ryomuk/tangnano-5V/applications/TangNano8080MEM/images/upd8080afc_3MHz.jpg

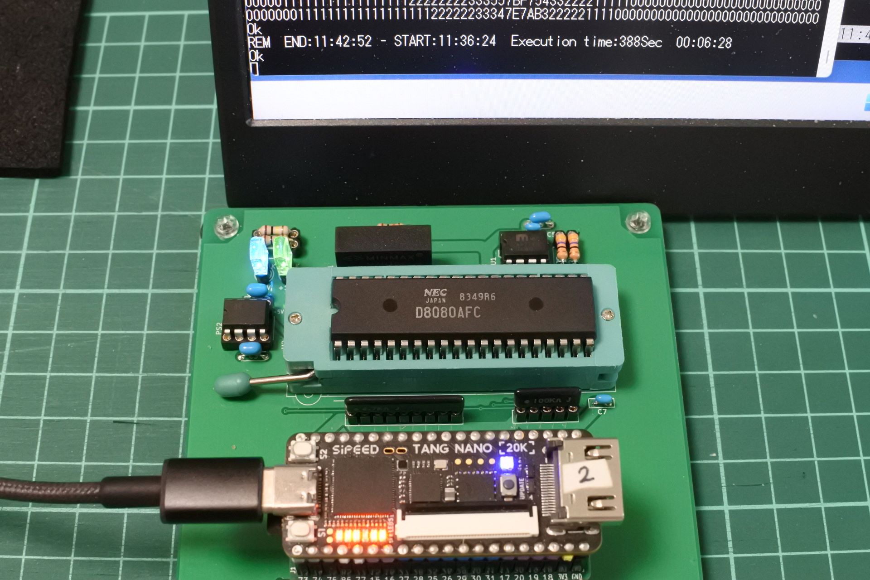
applications/TangNano8080MEM/images/upd8080afc_3MHz.jpg
