ryomuk/tangnano-5V/images/asciiart_12MHz.png

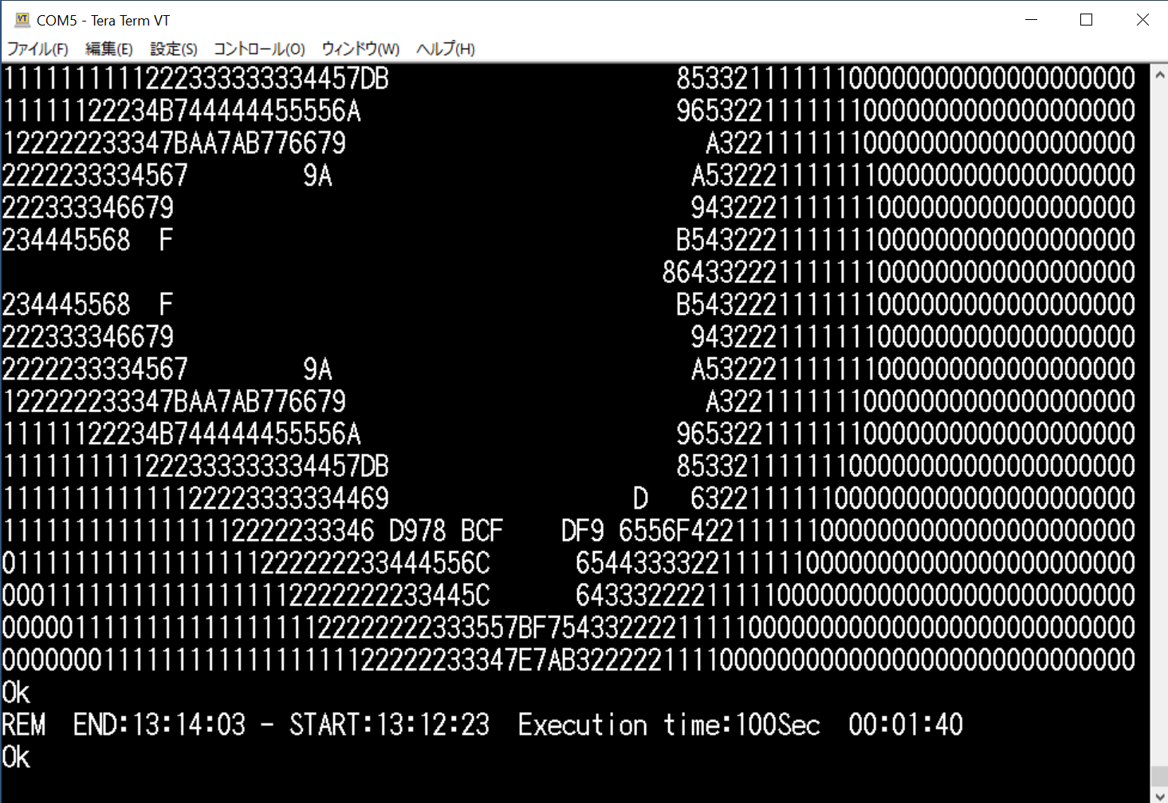
images/asciiart_12MHz.png
