ryomuk/tangnano-5V/images/tn20k5vrev1_1.jpg

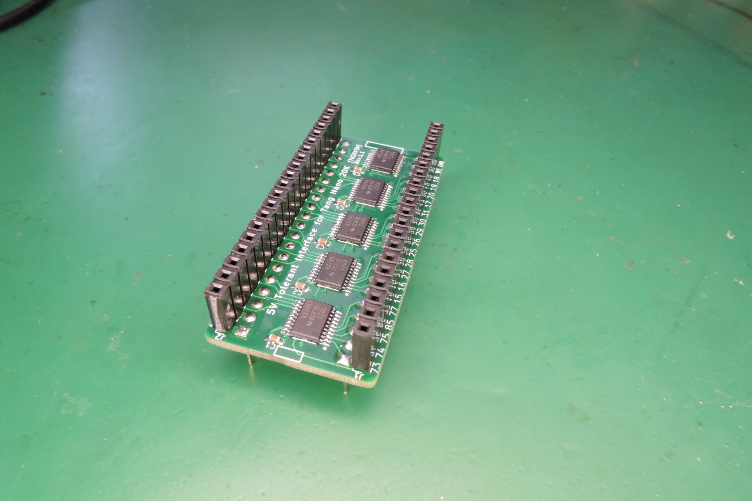
images/tn20k5vrev1_1.jpg
