ryomuk/tangnano-5V/hardware/9k/old/rev2.0/TangNano9K5V_pcb.pdf

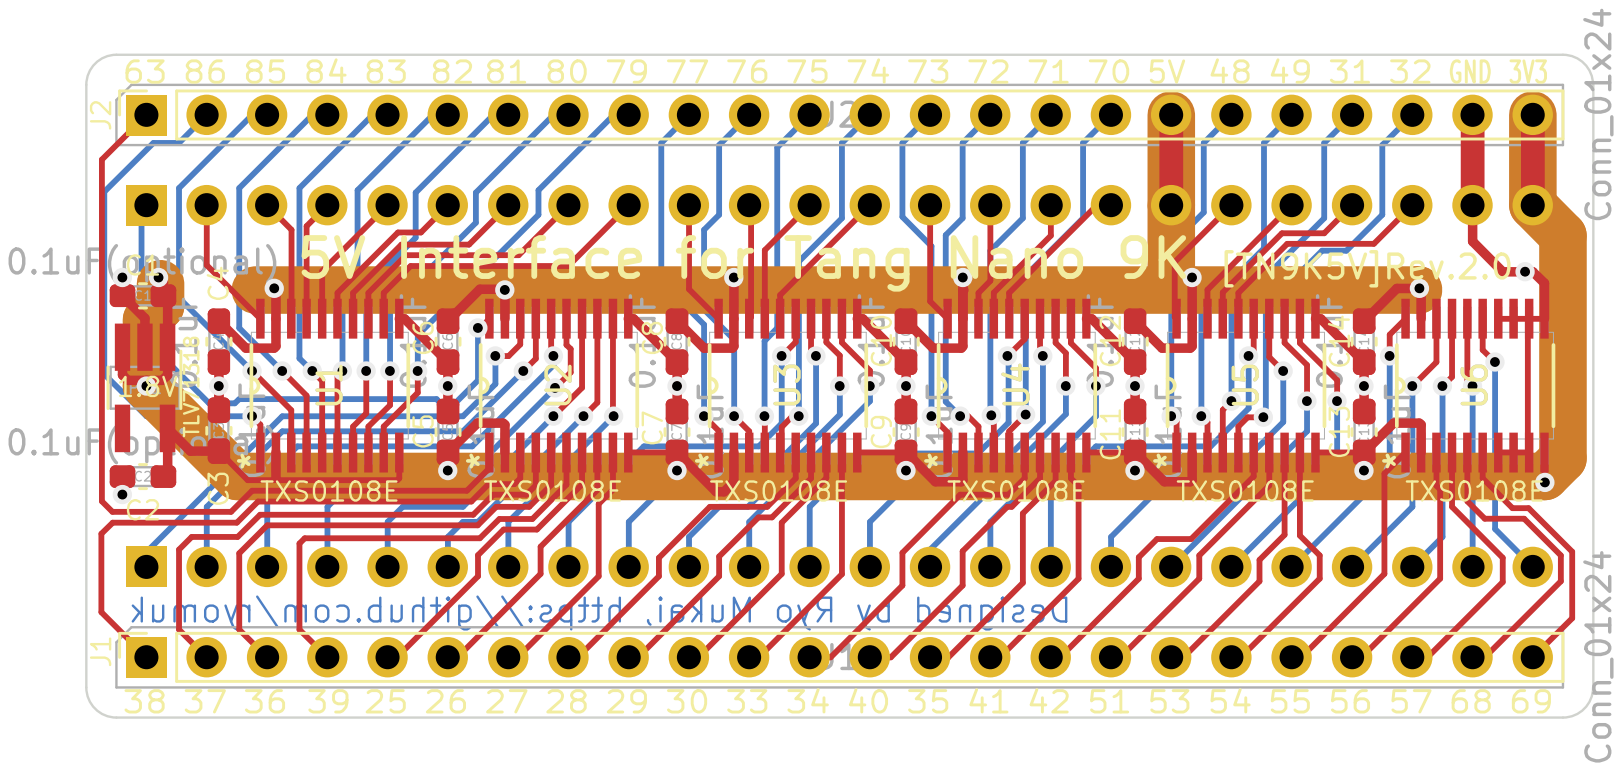
[picture p50: page 1]
