ryomuk/tangnano-5V/hardware/9k/old/rev2.0/TangNano9K5V_sch.pdf

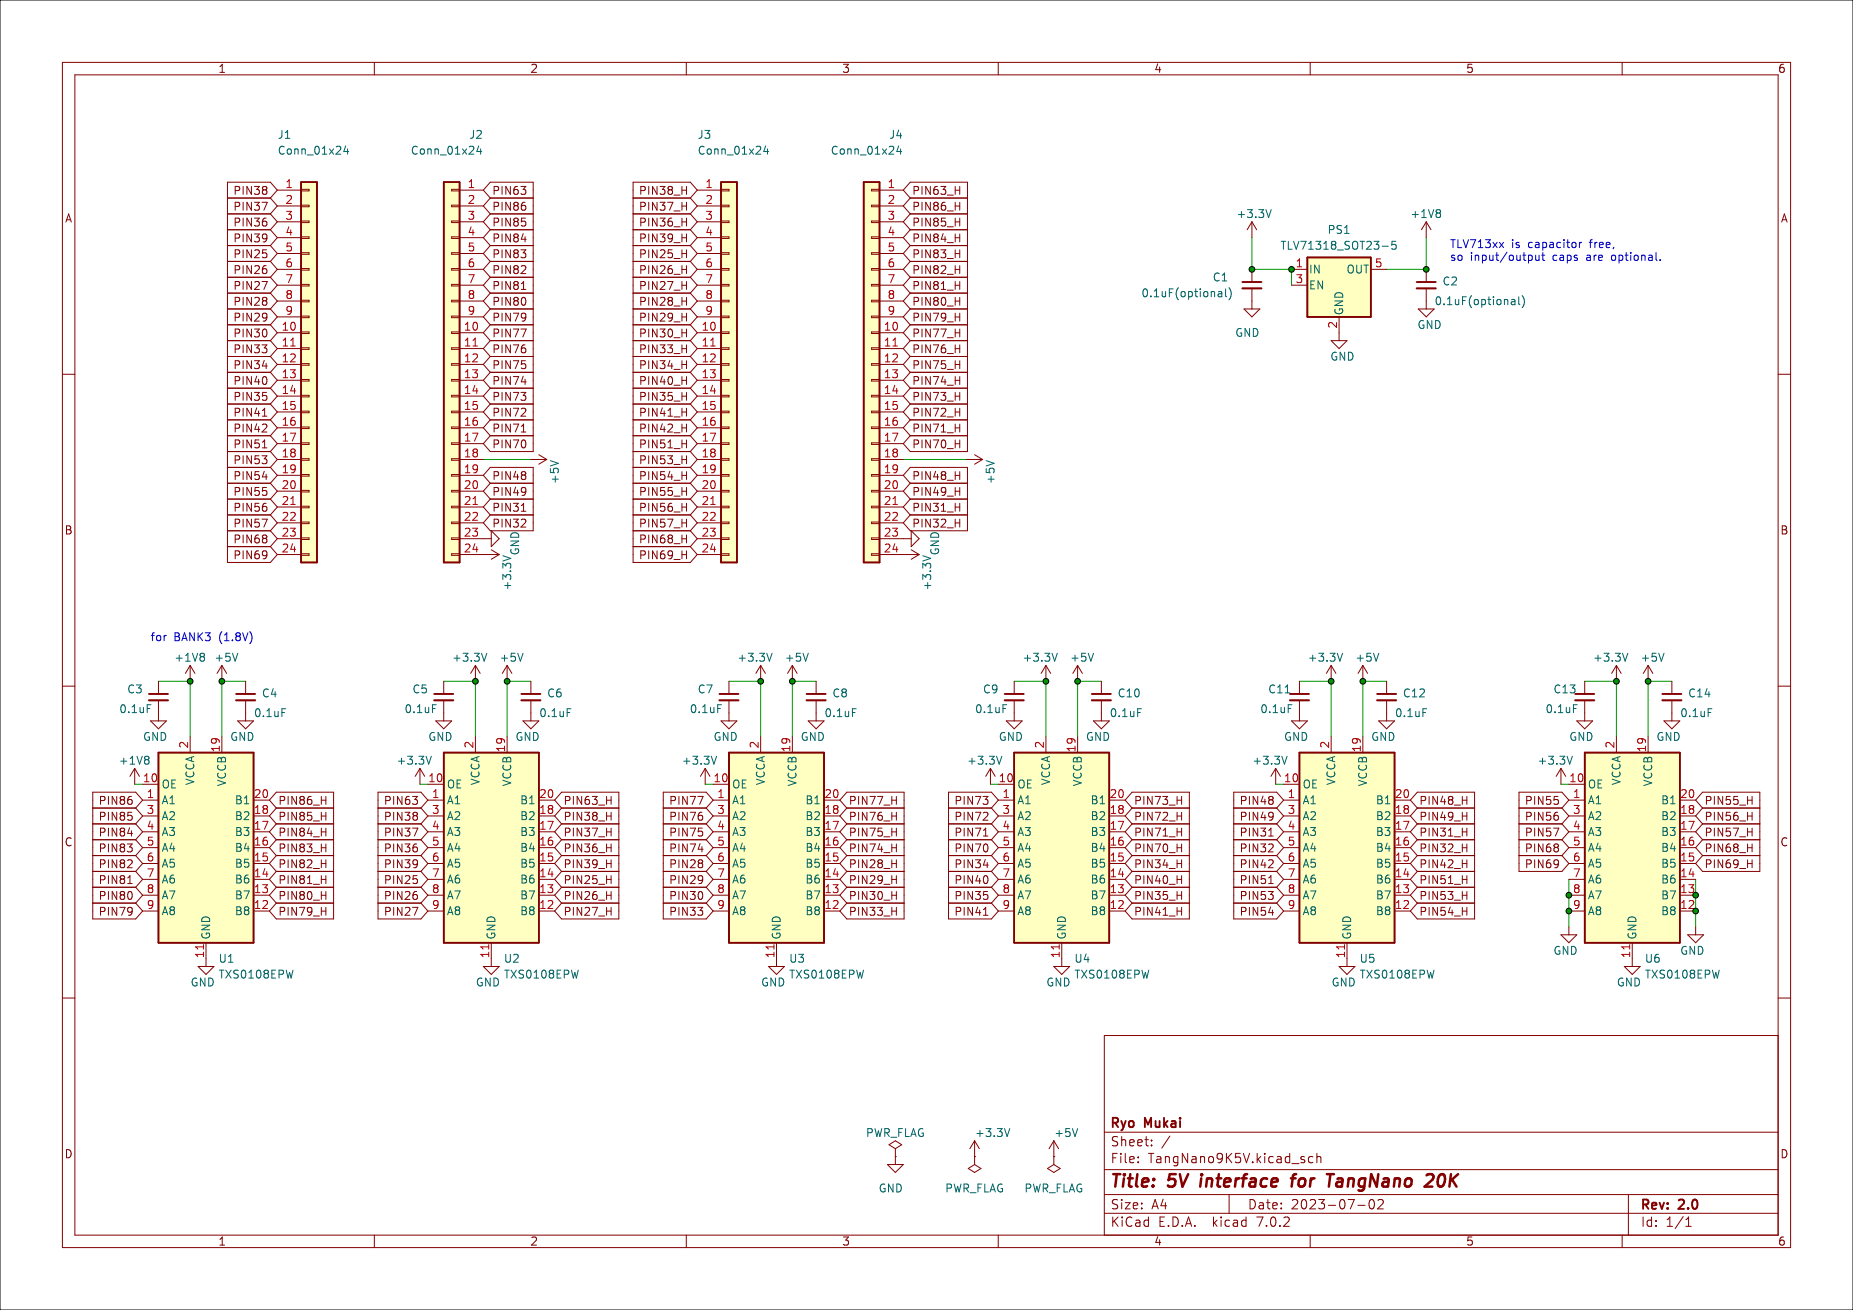
[picture p51: page 1]
