ryomuk/tangnano-5V/hardware/20k/old/rev1.1/TangNano5V_pcb.pdf

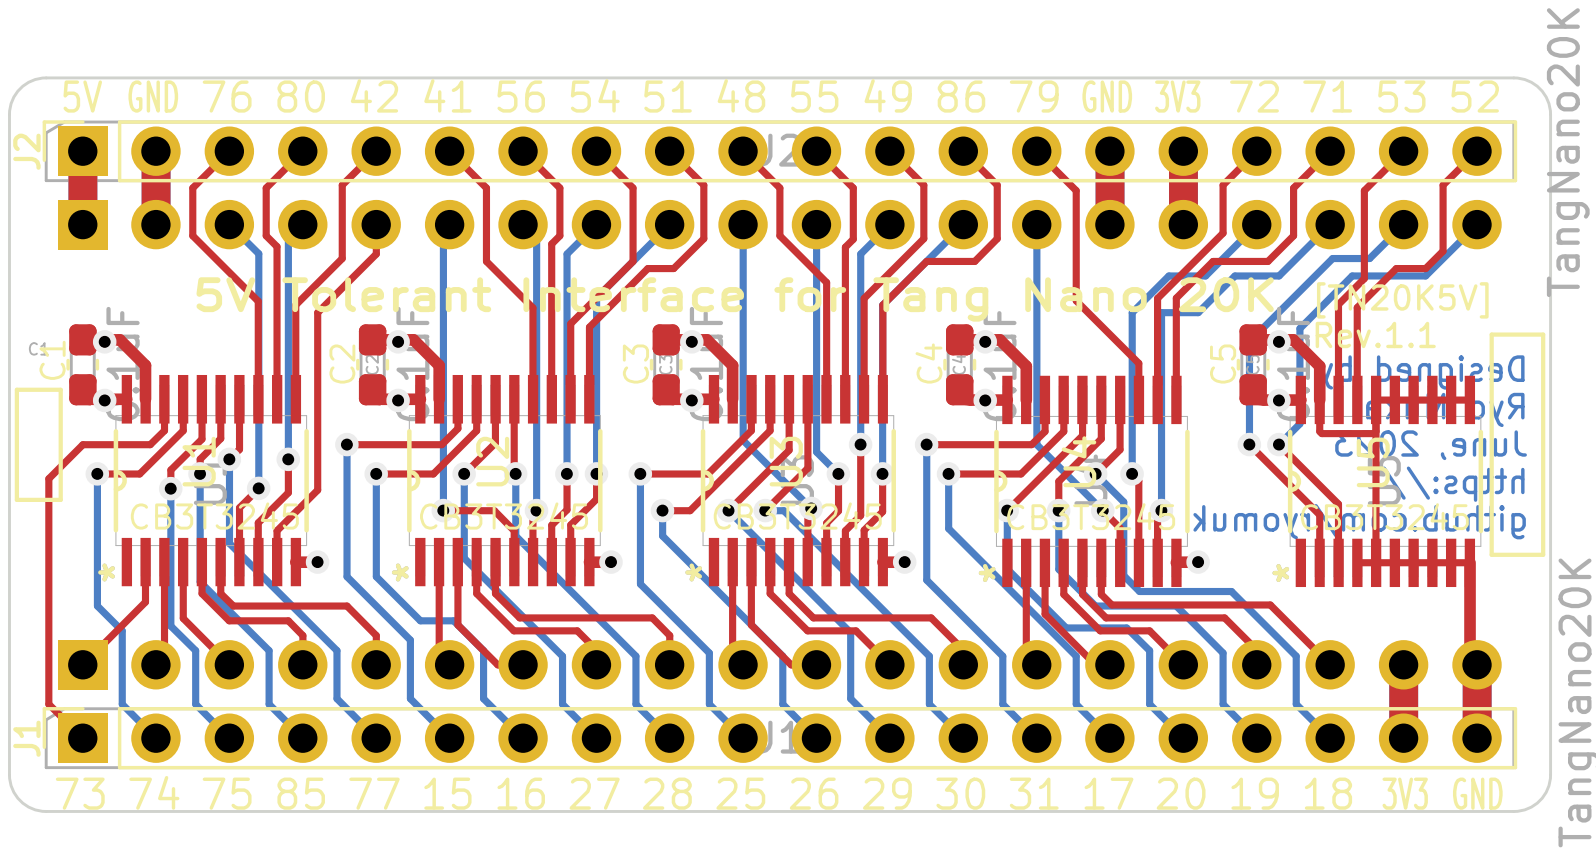
[picture p52: page 1]
