ryomuk/tangnano-5V/applications/TangNano8070MEM/rev1.0/TangNano8070MEM.kicad_sch

## KiCad design applications/TangNano8070MEM/rev1.0/TangNano8070MEM.kicad_sch (2023-07-23)

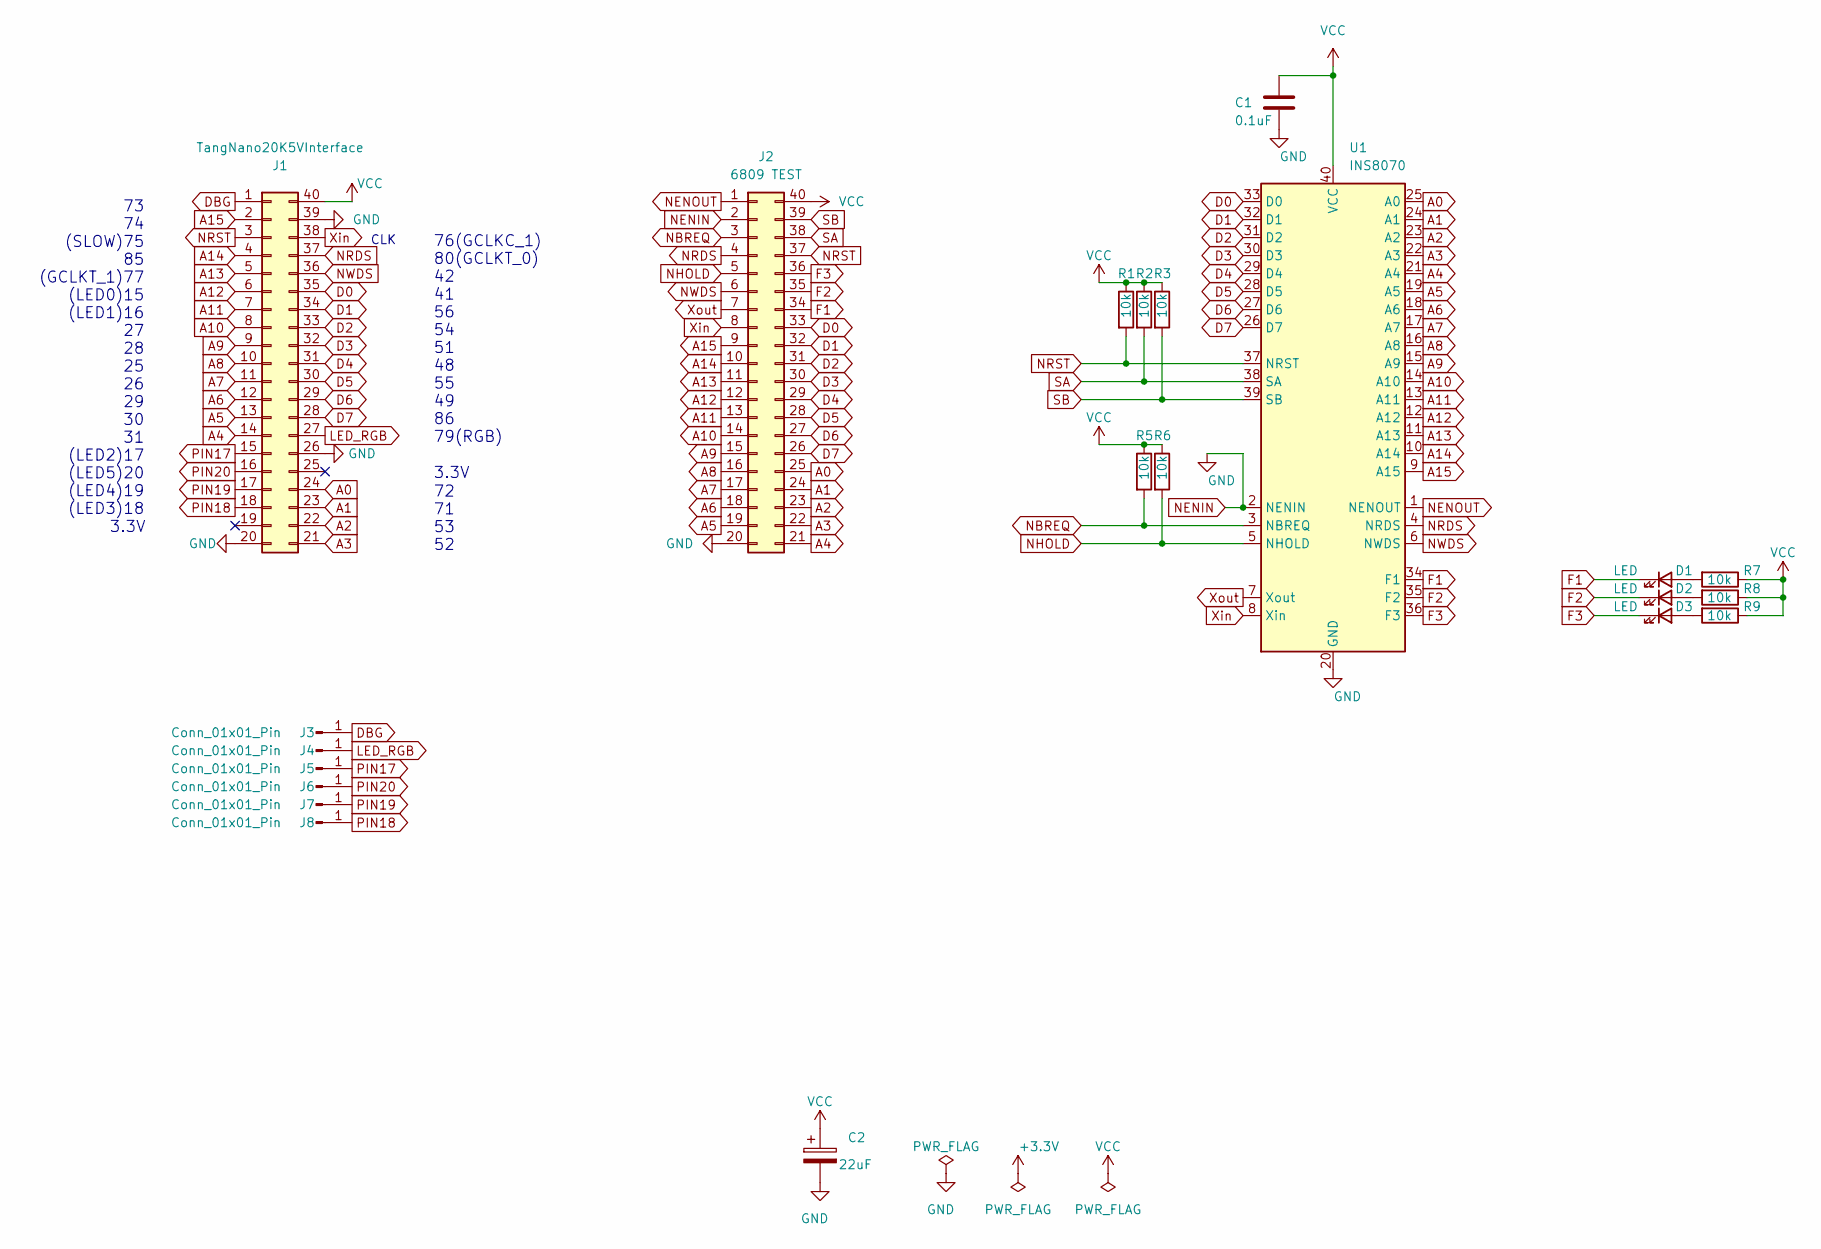
[picture p66: schematic TangNano8070MEM.kicad_sch]

Parts:
C1: 0.1uF; C_Disc_D4.3mm_W1.9mm_P5.00mm
C2: 22uF; CP_Radial_D4.0mm_P1.50mm
D1, D2, D3: LED; LED_D3.0mm
J1: TangNano20K5VInterface; DIP-40_W15.24mm_Socket
J2: 6809 TEST; DIP-40_W20.32mm800mil_Socket
J3, J4, J5, J6, J7, J8: Conn_01x01_Pin; PinHeader_1x01_P2.54mm_Vertical
R1, R2, R3, R5, R6, R7, R8, R9: 10k; R_Axial_DIN0207_L6.3mm_D2.5mm_P7.62mm_Horizontal
U1: INS8070; DIP-40_W15.24mm

Connections:
A0: J1.24, J2.25, U1.25 (A0)
A1: J1.23, J2.24, U1.24 (A1)
A2: J1.22, J2.23, U1.23 (A2)
A3: J1.21, J2.22, U1.22 (A3)
A4: J1.14, J2.21, U1.21 (A4)
A5: J1.13, J2.19, U1.19 (A5)
A6: J1.12, J2.18, U1.18 (A6)
A7: J1.11, J2.17, U1.17 (A7)
A8: J1.10, J2.16, U1.16 (A8)
A9: J1.9, J2.15, U1.15 (A9)
A10: J1.8, J2.14, U1.14 (A10)
A11: J1.7, J2.13, U1.13 (A11)
A12: J1.6, J2.12, U1.12 (A12)
A13: J1.5, J2.11, U1.11 (A13)
A14: J1.4, J2.10, U1.10 (A14)
A15: J1.2, J2.9, U1.9 (A15)
D0: J1.35, J2.33, U1.33 (D0)
D1: J1.34, J2.32, U1.32 (D1)
D2: J1.33, J2.31, U1.31 (D2)
D3: J1.32, J2.30, U1.30 (D3)
D4: J1.31, J2.29, U1.29 (D4)
D5: J1.30, J2.28, U1.28 (D5)
D6: J1.29, J2.27, U1.27 (D6)
D7: J1.28, J2.26, U1.26 (D7)
DBG: J1.1, J3.1
F1: D1.1 (K), J2.34, U1.34 (F1)
F2: D2.1 (K), J2.35, U1.35 (F2)
F3: D3.1 (K), J2.36, U1.36 (F3)
GND: C1.2, C2.2, J1.20, J1.26, J1.39, J2.2, J2.20, U1.2 (NENIN), U1.20 (GND)
LED_RGB: J1.27, J4.1
NBREQ: J2.3, R5.2, U1.3 (NBREQ)
NENOUT: J2.1, U1.1 (NENOUT)
NHOLD: J2.5, R6.2, U1.5 (NHOLD)
NRDS: J1.37, J2.4, U1.4 (NRDS)
NRST: J1.3, J2.37, R1.2, U1.37 (NRST)
NWDS: J1.36, J2.6, U1.6 (NWDS)
unnamed: D1.2 (A), R7.2
unnamed: D2.2 (A), R8.2
unnamed: D3.2 (A), R9.2
PIN17: J1.15, J5.1
PIN18: J1.18, J8.1
PIN19: J1.17, J7.1
PIN20: J1.16, J6.1
SA: J2.38, R2.2, U1.38 (SA)
SB: J2.39, R3.2, U1.39 (SB)
VCC: C1.1, C2.1, J1.40, J2.40, R1.1, R2.1, R3.1, R5.1, R6.1, R7.1, R8.1, R9.1, U1.40 (VCC)
Xin: J1.38, J2.8, U1.8 (Xin)
Xout: J2.7, U1.7 (Xout)

Notes on the sheet:
72 71 53 52
73 74 (SLOW)75 85 (GCLKT_1)77 (LED0)15 (LED1)16 27 28 25 26 29 30 31 (LED2)17 (LED5)20 (LED4)19 (LED3)18
76(GCLKC_1) 80(GCLKT_0) 42 41 56 54 51 48 55 49 86 79(RGB)
3.3V
CLK
