ryomuk/tangnano-5V/applications/9K/TangNanoZ80MEM_9K/breadboard/TangNanoZ80MEM.kicad_sch

## KiCad design applications/9K/TangNanoZ80MEM_9K/breadboard/TangNanoZ80MEM.kicad_sch (2024-04-21)

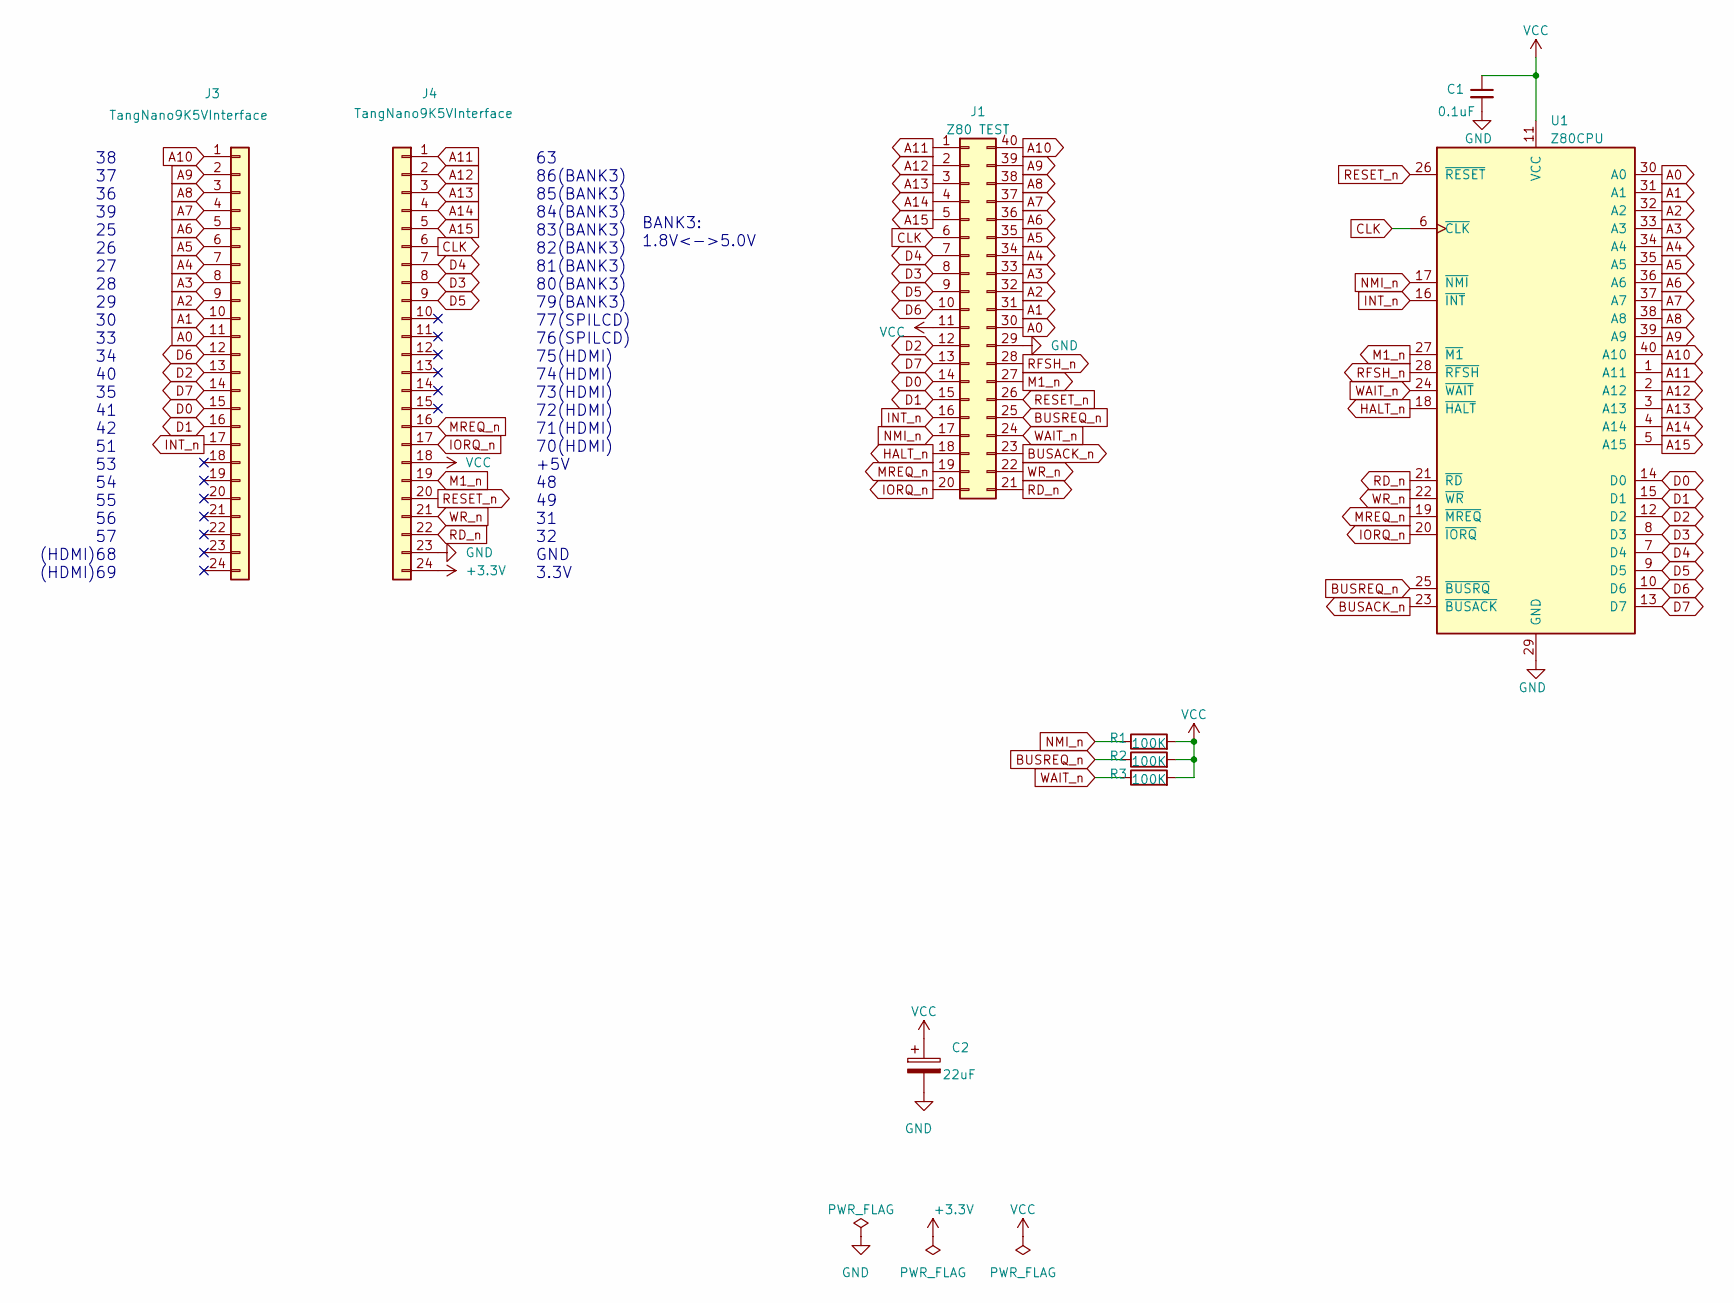
[picture p67: schematic TangNanoZ80MEM.kicad_sch]

Parts:
C1: 0.1uF; C_Disc_D4.3mm_W1.9mm_P5.00mm
C2: 22uF; CP_Radial_D4.0mm_P1.50mm
J1: Z80 TEST; DIP-40_W20.32mm800mil_Socket
J3, J4: TangNano9K5VInterface; PinHeader_1x24_P2.54mm_Vertical
R1, R2, R3: 100K
U1: Z80CPU; DIP-40_W15.24mm_Socket

Connections:
+3.3V: J4.24
A0: J1.30, J3.11, U1.30 (A0)
A1: J1.31, J3.10, U1.31 (A1)
A2: J1.32, J3.9, U1.32 (A2)
A3: J1.33, J3.8, U1.33 (A3)
A4: J1.34, J3.7, U1.34 (A4)
A5: J1.35, J3.6, U1.35 (A5)
A6: J1.36, J3.5, U1.36 (A6)
A7: J1.37, J3.4, U1.37 (A7)
A8: J1.38, J3.3, U1.38 (A8)
A9: J1.39, J3.2, U1.39 (A9)
A10: J1.40, J3.1, U1.40 (A10)
A11: J1.1, J4.1, U1.1 (A11)
A12: J1.2, J4.2, U1.2 (A12)
A13: J1.3, J4.3, U1.3 (A13)
A14: J1.4, J4.4, U1.4 (A14)
A15: J1.5, J4.5, U1.5 (A15)
BUSACK_n: J1.23, U1.23 (~BUSACK)
BUSREQ_n: J1.25, R2.1, U1.25 (~BUSRQ)
CLK: J1.6, J4.6, U1.6 (~CLK)
D0: J1.14, J3.15, U1.14 (D0)
D1: J1.15, J3.16, U1.15 (D1)
D2: J1.12, J3.13, U1.12 (D2)
D3: J1.8, J4.8, U1.8 (D3)
D4: J1.7, J4.7, U1.7 (D4)
D5: J1.9, J4.9, U1.9 (D5)
D6: J1.10, J3.12, U1.10 (D6)
D7: J1.13, J3.14, U1.13 (D7)
GND: C1.2, C2.2, J1.29, J4.23, U1.29 (GND)
HALT_n: J1.18, U1.18 (~HALT)
INT_n: J1.16, J3.17, U1.16 (~INT)
IORQ_n: J1.20, J4.17, U1.20 (~IORQ)
M1_n: J1.27, J4.19, U1.27 (~M1)
MREQ_n: J1.19, J4.16, U1.19 (~MREQ)
NMI_n: J1.17, R1.1, U1.17 (~NMI)
RD_n: J1.21, J4.22, U1.21 (~RD)
RESET_n: J1.26, J4.20, U1.26 (~RESET)
RFSH_n: J1.28, U1.28 (~RFSH)
VCC: C1.1, C2.1, J1.11, J4.18, R1.2, R2.2, R3.2, U1.11 (VCC)
WAIT_n: J1.24, R3.1, U1.24 (~WAIT)
WR_n: J1.22, J4.21, U1.22 (~WR)

Notes on the sheet:
38 37 36 39 25 26 27 28 29 30 33 34 40 35 41 42 51 53 54 55 56 57 (HDMI)68 (HDMI)69
BANK3: 1.8V<->5.0V
63 86(BANK3) 85(BANK3) 84(BANK3) 83(BANK3) 82(BANK3) 81(BANK3) 80(BANK3) 79(BANK3) 77(SPILCD) 76(SPILCD) 75(HDMI) 74(HDMI) 73(HDMI) 72(HDMI) 71(HDMI) 70(HDMI) +5V 48 49 31 32 GND 3.3V
