ryomuk/tangnano-5V/applications/TangNano8080MEM/TangNano8080MEM_project/src/rom.unimon.v

// rom.unimon.v
// to be included from the top module at the comple
//
// This file is generated from 
// unimon-20230319/8080
// https://electrelic.com/electrelic/node/1318
//
// MIT License
// 
// Copyright (c) 2019,2020,2021 Haruo Asano
// 
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
initial
begin
    mem['h0000]=8'hF3; mem['h0001]=8'hC3; mem['h0002]=8'h00; mem['h0003]=8'h01;
    mem['h0004]=8'hFF; mem['h0005]=8'hFF; mem['h0006]=8'hFF; mem['h0007]=8'hFF;
    mem['h0008]=8'hFF; mem['h0009]=8'hFF; mem['h000A]=8'hFF; mem['h000B]=8'hFF;
    mem['h000C]=8'hFF; mem['h000D]=8'hFF; mem['h000E]=8'hFF; mem['h000F]=8'hFF;
    mem['h0010]=8'hC3; mem['h0011]=8'hBC; mem['h0012]=8'h09; mem['h0013]=8'hFF;
    mem['h0014]=8'hFF; mem['h0015]=8'hFF; mem['h0016]=8'hFF; mem['h0017]=8'hFF;
    mem['h0018]=8'hC3; mem['h0019]=8'hA7; mem['h001A]=8'h06; mem['h001B]=8'hFF;
    mem['h001C]=8'hFF; mem['h001D]=8'hFF; mem['h001E]=8'hFF; mem['h001F]=8'hFF;
    mem['h0020]=8'hC3; mem['h0021]=8'hAD; mem['h0022]=8'h09; mem['h0023]=8'hFF;
    mem['h0024]=8'hFF; mem['h0025]=8'hFF; mem['h0026]=8'hFF; mem['h0027]=8'hFF;
    mem['h0028]=8'hC3; mem['h0029]=8'hB7; mem['h002A]=8'h09; mem['h002B]=8'hFF;
    mem['h002C]=8'hFF; mem['h002D]=8'hFF; mem['h002E]=8'hFF; mem['h002F]=8'hFF;
    mem['h0030]=8'hC3; mem['h0031]=8'hB6; mem['h0032]=8'h07; mem['h0033]=8'hFF;
    mem['h0034]=8'hFF; mem['h0035]=8'hFF; mem['h0036]=8'hFF; mem['h0037]=8'hFF;
    mem['h0038]=8'hC3; mem['h0039]=8'hE1; mem['h003A]=8'h07; mem['h003B]=8'hFF;
    mem['h003C]=8'hFF; mem['h003D]=8'hFF; mem['h003E]=8'hFF; mem['h003F]=8'hFF;
    mem['h0040]=8'hFF; mem['h0041]=8'hFF; mem['h0042]=8'hFF; mem['h0043]=8'hFF;
    mem['h0044]=8'hFF; mem['h0045]=8'hFF; mem['h0046]=8'hFF; mem['h0047]=8'hFF;
    mem['h0048]=8'hFF; mem['h0049]=8'hFF; mem['h004A]=8'hFF; mem['h004B]=8'hFF;
    mem['h004C]=8'hFF; mem['h004D]=8'hFF; mem['h004E]=8'hFF; mem['h004F]=8'hFF;
    mem['h0050]=8'hFF; mem['h0051]=8'hFF; mem['h0052]=8'hFF; mem['h0053]=8'hFF;
    mem['h0054]=8'hFF; mem['h0055]=8'hFF; mem['h0056]=8'hFF; mem['h0057]=8'hFF;
    mem['h0058]=8'hFF; mem['h0059]=8'hFF; mem['h005A]=8'hFF; mem['h005B]=8'hFF;
    mem['h005C]=8'hFF; mem['h005D]=8'hFF; mem['h005E]=8'hFF; mem['h005F]=8'hFF;
    mem['h0060]=8'hFF; mem['h0061]=8'hFF; mem['h0062]=8'hFF; mem['h0063]=8'hFF;
    mem['h0064]=8'hFF; mem['h0065]=8'hFF; mem['h0066]=8'hFF; mem['h0067]=8'hFF;
    mem['h0068]=8'hFF; mem['h0069]=8'hFF; mem['h006A]=8'hFF; mem['h006B]=8'hFF;
    mem['h006C]=8'hFF; mem['h006D]=8'hFF; mem['h006E]=8'hFF; mem['h006F]=8'hFF;
    mem['h0070]=8'hFF; mem['h0071]=8'hFF; mem['h0072]=8'hFF; mem['h0073]=8'hFF;
    mem['h0074]=8'hFF; mem['h0075]=8'hFF; mem['h0076]=8'hFF; mem['h0077]=8'hFF;
    mem['h0078]=8'hFF; mem['h0079]=8'hFF; mem['h007A]=8'hFF; mem['h007B]=8'hFF;
    mem['h007C]=8'hFF; mem['h007D]=8'hFF; mem['h007E]=8'hFF; mem['h007F]=8'hFF;
    mem['h0080]=8'hC3; mem['h0081]=8'h00; mem['h0082]=8'h01; mem['h0083]=8'hFF;
    mem['h0084]=8'hFF; mem['h0085]=8'hFF; mem['h0086]=8'hFF; mem['h0087]=8'hFF;
    mem['h0088]=8'hC3; mem['h0089]=8'h75; mem['h008A]=8'h01; mem['h008B]=8'hFF;
    mem['h008C]=8'hFF; mem['h008D]=8'hFF; mem['h008E]=8'hFF; mem['h008F]=8'hFF;
    mem['h0090]=8'hC3; mem['h0091]=8'hBC; mem['h0092]=8'h09; mem['h0093]=8'hFF;
    mem['h0094]=8'hFF; mem['h0095]=8'hFF; mem['h0096]=8'hFF; mem['h0097]=8'hFF;
    mem['h0098]=8'hC3; mem['h0099]=8'hA7; mem['h009A]=8'h06; mem['h009B]=8'hFF;
    mem['h009C]=8'hFF; mem['h009D]=8'hFF; mem['h009E]=8'hFF; mem['h009F]=8'hFF;
    mem['h00A0]=8'hC3; mem['h00A1]=8'hAD; mem['h00A2]=8'h09; mem['h00A3]=8'hFF;
    mem['h00A4]=8'hFF; mem['h00A5]=8'hFF; mem['h00A6]=8'hFF; mem['h00A7]=8'hFF;
    mem['h00A8]=8'hC3; mem['h00A9]=8'hB7; mem['h00AA]=8'h09; mem['h00AB]=8'hFF;
    mem['h00AC]=8'hFF; mem['h00AD]=8'hFF; mem['h00AE]=8'hFF; mem['h00AF]=8'hFF;
    mem['h00B0]=8'hFF; mem['h00B1]=8'hFF; mem['h00B2]=8'hFF; mem['h00B3]=8'hFF;
    mem['h00B4]=8'hFF; mem['h00B5]=8'hFF; mem['h00B6]=8'hFF; mem['h00B7]=8'hFF;
    mem['h00B8]=8'hFF; mem['h00B9]=8'hFF; mem['h00BA]=8'hFF; mem['h00BB]=8'hFF;
    mem['h00BC]=8'hFF; mem['h00BD]=8'hFF; mem['h00BE]=8'hFF; mem['h00BF]=8'hFF;
    mem['h00C0]=8'hFF; mem['h00C1]=8'hFF; mem['h00C2]=8'hFF; mem['h00C3]=8'hFF;
    mem['h00C4]=8'hFF; mem['h00C5]=8'hFF; mem['h00C6]=8'hFF; mem['h00C7]=8'hFF;
    mem['h00C8]=8'hFF; mem['h00C9]=8'hFF; mem['h00CA]=8'hFF; mem['h00CB]=8'hFF;
    mem['h00CC]=8'hFF; mem['h00CD]=8'hFF; mem['h00CE]=8'hFF; mem['h00CF]=8'hFF;
    mem['h00D0]=8'hFF; mem['h00D1]=8'hFF; mem['h00D2]=8'hFF; mem['h00D3]=8'hFF;
    mem['h00D4]=8'hFF; mem['h00D5]=8'hFF; mem['h00D6]=8'hFF; mem['h00D7]=8'hFF;
    mem['h00D8]=8'hFF; mem['h00D9]=8'hFF; mem['h00DA]=8'hFF; mem['h00DB]=8'hFF;
    mem['h00DC]=8'hFF; mem['h00DD]=8'hFF; mem['h00DE]=8'hFF; mem['h00DF]=8'hFF;
    mem['h00E0]=8'hFF; mem['h00E1]=8'hFF; mem['h00E2]=8'hFF; mem['h00E3]=8'hFF;
    mem['h00E4]=8'hFF; mem['h00E5]=8'hFF; mem['h00E6]=8'hFF; mem['h00E7]=8'hFF;
    mem['h00E8]=8'hFF; mem['h00E9]=8'hFF; mem['h00EA]=8'hFF; mem['h00EB]=8'hFF;
    mem['h00EC]=8'hFF; mem['h00ED]=8'hFF; mem['h00EE]=8'hFF; mem['h00EF]=8'hFF;
    mem['h00F0]=8'hFF; mem['h00F1]=8'hFF; mem['h00F2]=8'hFF; mem['h00F3]=8'hFF;
    mem['h00F4]=8'hFF; mem['h00F5]=8'hFF; mem['h00F6]=8'hFF; mem['h00F7]=8'hFF;
    mem['h00F8]=8'hFF; mem['h00F9]=8'hFF; mem['h00FA]=8'hFF; mem['h00FB]=8'hFF;
    mem['h00FC]=8'hFF; mem['h00FD]=8'hFF; mem['h00FE]=8'hFF; mem['h00FF]=8'hFF;
    mem['h0100]=8'h31; mem['h0101]=8'h00; mem['h0102]=8'h00; mem['h0103]=8'hCD;
    mem['h0104]=8'h94; mem['h0105]=8'h09; mem['h0106]=8'h21; mem['h0107]=8'h00;
    mem['h0108]=8'h80; mem['h0109]=8'h22; mem['h010A]=8'h10; mem['h010B]=8'hFF;
    mem['h010C]=8'h22; mem['h010D]=8'h17; mem['h010E]=8'hFF; mem['h010F]=8'h22;
    mem['h0110]=8'h15; mem['h0111]=8'hFF; mem['h0112]=8'h3E; mem['h0113]=8'h49;
    mem['h0114]=8'h32; mem['h0115]=8'h19; mem['h0116]=8'hFF; mem['h0117]=8'hAF;
    mem['h0118]=8'h32; mem['h0119]=8'h1B; mem['h011A]=8'hFF; mem['h011B]=8'h21;
    mem['h011C]=8'h1C; mem['h011D]=8'hFF; mem['h011E]=8'h0E; mem['h011F]=8'h0C;
    mem['h0120]=8'hAF; mem['h0121]=8'h77; mem['h0122]=8'h23; mem['h0123]=8'h0D;
    mem['h0124]=8'hC2; mem['h0125]=8'h21; mem['h0126]=8'h01; mem['h0127]=8'h21;
    mem['h0128]=8'h00; mem['h0129]=8'h00; mem['h012A]=8'h22; mem['h012B]=8'h23;
    mem['h012C]=8'hFF; mem['h012D]=8'h21; mem['h012E]=8'h00; mem['h012F]=8'h80;
    mem['h0130]=8'h22; mem['h0131]=8'h25; mem['h0132]=8'hFF; mem['h0133]=8'h21;
    mem['h0134]=8'h12; mem['h0135]=8'h08; mem['h0136]=8'hCD; mem['h0137]=8'hA7;
    mem['h0138]=8'h06; mem['h0139]=8'h3E; mem['h013A]=8'h7F; mem['h013B]=8'h3C;
    mem['h013C]=8'hEA; mem['h013D]=8'h6A; mem['h013E]=8'h01; mem['h013F]=8'hF5;
    mem['h0140]=8'hC1; mem['h0141]=8'h79; mem['h0142]=8'hE6; mem['h0143]=8'h08;
    mem['h0144]=8'hC2; mem['h0145]=8'h5A; mem['h0146]=8'h01; mem['h0147]=8'h21;
    mem['h0148]=8'hFF; mem['h0149]=8'hFF; mem['h014A]=8'h23; mem['h014B]=8'hF5;
    mem['h014C]=8'hC1; mem['h014D]=8'h79; mem['h014E]=8'hE6; mem['h014F]=8'h20;
    mem['h0150]=8'hC2; mem['h0151]=8'h62; mem['h0152]=8'h01; mem['h0153]=8'h21;
    mem['h0154]=8'h74; mem['h0155]=8'h08; mem['h0156]=8'hAF; mem['h0157]=8'hC3;
    mem['h0158]=8'h6F; mem['h0159]=8'h01; mem['h015A]=8'h21; mem['h015B]=8'h7C;
    mem['h015C]=8'h08; mem['h015D]=8'h3E; mem['h015E]=8'h01; mem['h015F]=8'hC3;
    mem['h0160]=8'h6F; mem['h0161]=8'h01; mem['h0162]=8'h21; mem['h0163]=8'h87;
    mem['h0164]=8'h08; mem['h0165]=8'h3E; mem['h0166]=8'h02; mem['h0167]=8'hC3;
    mem['h0168]=8'h6F; mem['h0169]=8'h01; mem['h016A]=8'h21; mem['h016B]=8'h8F;
    mem['h016C]=8'h08; mem['h016D]=8'h3E; mem['h016E]=8'h10; mem['h016F]=8'h32;
    mem['h0170]=8'h1B; mem['h0171]=8'hFF; mem['h0172]=8'hCD; mem['h0173]=8'hA7;
    mem['h0174]=8'h06; mem['h0175]=8'h21; mem['h0176]=8'h2D; mem['h0177]=8'h08;
    mem['h0178]=8'hCD; mem['h0179]=8'hA7; mem['h017A]=8'h06; mem['h017B]=8'hCD;
    mem['h017C]=8'h02; mem['h017D]=8'h07; mem['h017E]=8'h21; mem['h017F]=8'h00;
    mem['h0180]=8'hFF; mem['h0181]=8'hCD; mem['h0182]=8'h58; mem['h0183]=8'h07;
    mem['h0184]=8'hCD; mem['h0185]=8'h60; mem['h0186]=8'h07; mem['h0187]=8'hB7;
    mem['h0188]=8'hCA; mem['h0189]=8'h75; mem['h018A]=8'h01; mem['h018B]=8'hFE;
    mem['h018C]=8'h44; mem['h018D]=8'hCA; mem['h018E]=8'hBC; mem['h018F]=8'h01;
    mem['h0190]=8'hFE; mem['h0191]=8'h47; mem['h0192]=8'hCA; mem['h0193]=8'hE4;
    mem['h0194]=8'h02; mem['h0195]=8'hFE; mem['h0196]=8'h53; mem['h0197]=8'hCA;
    mem['h0198]=8'h1A; mem['h0199]=8'h03; mem['h019A]=8'hFE; mem['h019B]=8'h4C;
    mem['h019C]=8'hCA; mem['h019D]=8'h87; mem['h019E]=8'h03; mem['h019F]=8'hFE;
    mem['h01A0]=8'h50; mem['h01A1]=8'hCA; mem['h01A2]=8'h6D; mem['h01A3]=8'h04;
    mem['h01A4]=8'hFE; mem['h01A5]=8'h49; mem['h01A6]=8'hCA; mem['h01A7]=8'h75;
    mem['h01A8]=8'h05; mem['h01A9]=8'hFE; mem['h01AA]=8'h4F; mem['h01AB]=8'hCA;
    mem['h01AC]=8'h9F; mem['h01AD]=8'h05; mem['h01AE]=8'hFE; mem['h01AF]=8'h52;
    mem['h01B0]=8'hCA; mem['h01B1]=8'hDA; mem['h01B2]=8'h05; mem['h01B3]=8'h21;
    mem['h01B4]=8'h30; mem['h01B5]=8'h08; mem['h01B6]=8'hCD; mem['h01B7]=8'hA7;
    mem['h01B8]=8'h06; mem['h01B9]=8'hC3; mem['h01BA]=8'h75; mem['h01BB]=8'h01;
    mem['h01BC]=8'h23; mem['h01BD]=8'hCD; mem['h01BE]=8'h58; mem['h01BF]=8'h07;
    mem['h01C0]=8'hCD; mem['h01C1]=8'h69; mem['h01C2]=8'h07; mem['h01C3]=8'h79;
    mem['h01C4]=8'hB7; mem['h01C5]=8'hC2; mem['h01C6]=8'hDD; mem['h01C7]=8'h01;
    mem['h01C8]=8'hCD; mem['h01C9]=8'h58; mem['h01CA]=8'h07; mem['h01CB]=8'h7E;
    mem['h01CC]=8'hB7; mem['h01CD]=8'hC2; mem['h01CE]=8'hB3; mem['h01CF]=8'h01;
    mem['h01D0]=8'h2A; mem['h01D1]=8'h10; mem['h01D2]=8'hFF; mem['h01D3]=8'h01;
    mem['h01D4]=8'h80; mem['h01D5]=8'h00; mem['h01D6]=8'h09; mem['h01D7]=8'h22;
    mem['h01D8]=8'h12; mem['h01D9]=8'hFF; mem['h01DA]=8'hC3; mem['h01DB]=8'h13;
    mem['h01DC]=8'h02; mem['h01DD]=8'hEB; mem['h01DE]=8'h22; mem['h01DF]=8'h10;
    mem['h01E0]=8'hFF; mem['h01E1]=8'hEB; mem['h01E2]=8'hCD; mem['h01E3]=8'h58;
    mem['h01E4]=8'h07; mem['h01E5]=8'h7E; mem['h01E6]=8'hFE; mem['h01E7]=8'h2C;
    mem['h01E8]=8'hCA; mem['h01E9]=8'hF9; mem['h01EA]=8'h01; mem['h01EB]=8'hB7;
    mem['h01EC]=8'hC2; mem['h01ED]=8'hB3; mem['h01EE]=8'h01; mem['h01EF]=8'h21;
    mem['h01F0]=8'h80; mem['h01F1]=8'h00; mem['h01F2]=8'h19; mem['h01F3]=8'h22;
    mem['h01F4]=8'h12; mem['h01F5]=8'hFF; mem['h01F6]=8'hC3; mem['h01F7]=8'h13;
    mem['h01F8]=8'h02; mem['h01F9]=8'h23; mem['h01FA]=8'hCD; mem['h01FB]=8'h58;
    mem['h01FC]=8'h07; mem['h01FD]=8'hCD; mem['h01FE]=8'h69; mem['h01FF]=8'h07;
    mem['h0200]=8'hCD; mem['h0201]=8'h58; mem['h0202]=8'h07; mem['h0203]=8'h79;
    mem['h0204]=8'hB7; mem['h0205]=8'hCA; mem['h0206]=8'hB3; mem['h0207]=8'h01;
    mem['h0208]=8'h7E; mem['h0209]=8'hB7; mem['h020A]=8'hC2; mem['h020B]=8'hB3;
    mem['h020C]=8'h01; mem['h020D]=8'h13; mem['h020E]=8'hEB; mem['h020F]=8'h22;
    mem['h0210]=8'h12; mem['h0211]=8'hFF; mem['h0212]=8'hEB; mem['h0213]=8'h2A;
    mem['h0214]=8'h10; mem['h0215]=8'hFF; mem['h0216]=8'h3E; mem['h0217]=8'hF0;
    mem['h0218]=8'hA5; mem['h0219]=8'h6F; mem['h021A]=8'hAF; mem['h021B]=8'h32;
    mem['h021C]=8'h14; mem['h021D]=8'hFF; mem['h021E]=8'hE5; mem['h021F]=8'hCD;
    mem['h0220]=8'h47; mem['h0221]=8'h02; mem['h0222]=8'hE1; mem['h0223]=8'h01;
    mem['h0224]=8'h10; mem['h0225]=8'h00; mem['h0226]=8'h09; mem['h0227]=8'hCD;
    mem['h0228]=8'hB7; mem['h0229]=8'h09; mem['h022A]=8'hC2; mem['h022B]=8'h3E;
    mem['h022C]=8'h02; mem['h022D]=8'h3A; mem['h022E]=8'h14; mem['h022F]=8'hFF;
    mem['h0230]=8'hFE; mem['h0231]=8'h02; mem['h0232]=8'hDA; mem['h0233]=8'h1E;
    mem['h0234]=8'h02; mem['h0235]=8'h2A; mem['h0236]=8'h12; mem['h0237]=8'hFF;
    mem['h0238]=8'h22; mem['h0239]=8'h10; mem['h023A]=8'hFF; mem['h023B]=8'hC3;
    mem['h023C]=8'h75; mem['h023D]=8'h01; mem['h023E]=8'hCD; mem['h023F]=8'hAD;
    mem['h0240]=8'h09; mem['h0241]=8'h22; mem['h0242]=8'h10; mem['h0243]=8'hFF;
    mem['h0244]=8'hC3; mem['h0245]=8'h75; mem['h0246]=8'h01; mem['h0247]=8'hCD;
    mem['h0248]=8'hB1; mem['h0249]=8'h06; mem['h024A]=8'hE5; mem['h024B]=8'h21;
    mem['h024C]=8'h38; mem['h024D]=8'h08; mem['h024E]=8'hCD; mem['h024F]=8'hA7;
    mem['h0250]=8'h06; mem['h0251]=8'h21; mem['h0252]=8'h00; mem['h0253]=8'hFF;
    mem['h0254]=8'h22; mem['h0255]=8'h28; mem['h0256]=8'hFF; mem['h0257]=8'hE1;
    mem['h0258]=8'h06; mem['h0259]=8'h10; mem['h025A]=8'hCD; mem['h025B]=8'h8A;
    mem['h025C]=8'h02; mem['h025D]=8'h05; mem['h025E]=8'hC2; mem['h025F]=8'h5A;
    mem['h0260]=8'h02; mem['h0261]=8'h21; mem['h0262]=8'h3B; mem['h0263]=8'h08;
    mem['h0264]=8'hCD; mem['h0265]=8'hA7; mem['h0266]=8'h06; mem['h0267]=8'h21;
    mem['h0268]=8'h00; mem['h0269]=8'hFF; mem['h026A]=8'h06; mem['h026B]=8'h10;
    mem['h026C]=8'h7E; mem['h026D]=8'h23; mem['h026E]=8'hFE; mem['h026F]=8'h20;
    mem['h0270]=8'hDA; mem['h0271]=8'h7E; mem['h0272]=8'h02; mem['h0273]=8'hFE;
    mem['h0274]=8'h7F; mem['h0275]=8'hD2; mem['h0276]=8'h7E; mem['h0277]=8'h02;
    mem['h0278]=8'hCD; mem['h0279]=8'hBC; mem['h027A]=8'h09; mem['h027B]=8'hC3;
    mem['h027C]=8'h83; mem['h027D]=8'h02; mem['h027E]=8'h3E; mem['h027F]=8'h2E;
    mem['h0280]=8'hCD; mem['h0281]=8'hBC; mem['h0282]=8'h09; mem['h0283]=8'h05;
    mem['h0284]=8'hC2; mem['h0285]=8'h6C; mem['h0286]=8'h02; mem['h0287]=8'hC3;
    mem['h0288]=8'hF8; mem['h0289]=8'h06; mem['h028A]=8'h3E; mem['h028B]=8'h20;
    mem['h028C]=8'hCD; mem['h028D]=8'hBC; mem['h028E]=8'h09; mem['h028F]=8'h3A;
    mem['h0290]=8'h14; mem['h0291]=8'hFF; mem['h0292]=8'hB7; mem['h0293]=8'hC2;
    mem['h0294]=8'hBD; mem['h0295]=8'h02; mem['h0296]=8'h3A; mem['h0297]=8'h10;
    mem['h0298]=8'hFF; mem['h0299]=8'hBD; mem['h029A]=8'hC2; mem['h029B]=8'hA4;
    mem['h029C]=8'h02; mem['h029D]=8'h3A; mem['h029E]=8'h11; mem['h029F]=8'hFF;
    mem['h02A0]=8'hBC; mem['h02A1]=8'hCA; mem['h02A2]=8'hB8; mem['h02A3]=8'h02;
    mem['h02A4]=8'h3E; mem['h02A5]=8'h20; mem['h02A6]=8'hCD; mem['h02A7]=8'hBC;
    mem['h02A8]=8'h09; mem['h02A9]=8'hCD; mem['h02AA]=8'hBC; mem['h02AB]=8'h09;
    mem['h02AC]=8'hE5; mem['h02AD]=8'h2A; mem['h02AE]=8'h28; mem['h02AF]=8'hFF;
    mem['h02B0]=8'h77; mem['h02B1]=8'h23; mem['h02B2]=8'h22; mem['h02B3]=8'h28;
    mem['h02B4]=8'hFF; mem['h02B5]=8'hE1; mem['h02B6]=8'h23; mem['h02B7]=8'hC9;
    mem['h02B8]=8'h3E; mem['h02B9]=8'h01; mem['h02BA]=8'h32; mem['h02BB]=8'h14;
    mem['h02BC]=8'hFF; mem['h02BD]=8'h3A; mem['h02BE]=8'h14; mem['h02BF]=8'hFF;
    mem['h02C0]=8'hFE; mem['h02C1]=8'h01; mem['h02C2]=8'hC2; mem['h02C3]=8'hA4;
    mem['h02C4]=8'h02; mem['h02C5]=8'h7E; mem['h02C6]=8'hE5; mem['h02C7]=8'h2A;
    mem['h02C8]=8'h28; mem['h02C9]=8'hFF; mem['h02CA]=8'h77; mem['h02CB]=8'h23;
    mem['h02CC]=8'h22; mem['h02CD]=8'h28; mem['h02CE]=8'hFF; mem['h02CF]=8'hE1;
    mem['h02D0]=8'hCD; mem['h02D1]=8'hB6; mem['h02D2]=8'h06; mem['h02D3]=8'h23;
    mem['h02D4]=8'h3A; mem['h02D5]=8'h12; mem['h02D6]=8'hFF; mem['h02D7]=8'hBD;
    mem['h02D8]=8'hC0; mem['h02D9]=8'h3A; mem['h02DA]=8'h13; mem['h02DB]=8'hFF;
    mem['h02DC]=8'hBC; mem['h02DD]=8'hC0; mem['h02DE]=8'h3E; mem['h02DF]=8'h02;
    mem['h02E0]=8'h32; mem['h02E1]=8'h14; mem['h02E2]=8'hFF; mem['h02E3]=8'hC9;
    mem['h02E4]=8'h23; mem['h02E5]=8'hCD; mem['h02E6]=8'h58; mem['h02E7]=8'h07;
    mem['h02E8]=8'hCD; mem['h02E9]=8'h69; mem['h02EA]=8'h07; mem['h02EB]=8'h7E;
    mem['h02EC]=8'hB7; mem['h02ED]=8'hC2; mem['h02EE]=8'hB3; mem['h02EF]=8'h01;
    mem['h02F0]=8'h79; mem['h02F1]=8'hB7; mem['h02F2]=8'hCA; mem['h02F3]=8'hFA;
    mem['h02F4]=8'h02; mem['h02F5]=8'h62; mem['h02F6]=8'h6B; mem['h02F7]=8'h22;
    mem['h02F8]=8'h25; mem['h02F9]=8'hFF; mem['h02FA]=8'h2A; mem['h02FB]=8'h23;
    mem['h02FC]=8'hFF; mem['h02FD]=8'hF9; mem['h02FE]=8'h2A; mem['h02FF]=8'h25;
    mem['h0300]=8'hFF; mem['h0301]=8'hE5; mem['h0302]=8'h3A; mem['h0303]=8'h27;
    mem['h0304]=8'hFF; mem['h0305]=8'h4F; mem['h0306]=8'h3A; mem['h0307]=8'h1C;
    mem['h0308]=8'hFF; mem['h0309]=8'h47; mem['h030A]=8'hC5; mem['h030B]=8'h21;
    mem['h030C]=8'h1D; mem['h030D]=8'hFF; mem['h030E]=8'h4E; mem['h030F]=8'h23;
    mem['h0310]=8'h46; mem['h0311]=8'h23; mem['h0312]=8'h5E; mem['h0313]=8'h23;
    mem['h0314]=8'h56; mem['h0315]=8'h2A; mem['h0316]=8'h21; mem['h0317]=8'hFF;
    mem['h0318]=8'hF1; mem['h0319]=8'hC9; mem['h031A]=8'h23; mem['h031B]=8'hCD;
    mem['h031C]=8'h58; mem['h031D]=8'h07; mem['h031E]=8'hCD; mem['h031F]=8'h69;
    mem['h0320]=8'h07; mem['h0321]=8'hCD; mem['h0322]=8'h58; mem['h0323]=8'h07;
    mem['h0324]=8'h7E; mem['h0325]=8'hB7; mem['h0326]=8'hC2; mem['h0327]=8'hB3;
    mem['h0328]=8'h01; mem['h0329]=8'hEB; mem['h032A]=8'h79; mem['h032B]=8'hB7;
    mem['h032C]=8'hC2; mem['h032D]=8'h32; mem['h032E]=8'h03; mem['h032F]=8'h2A;
    mem['h0330]=8'h17; mem['h0331]=8'hFF; mem['h0332]=8'hCD; mem['h0333]=8'hB1;
    mem['h0334]=8'h06; mem['h0335]=8'hE5; mem['h0336]=8'h21; mem['h0337]=8'h3B;
    mem['h0338]=8'h08; mem['h0339]=8'hCD; mem['h033A]=8'hA7; mem['h033B]=8'h06;
    mem['h033C]=8'hE1; mem['h033D]=8'h7E; mem['h033E]=8'hE5; mem['h033F]=8'hCD;
    mem['h0340]=8'hB6; mem['h0341]=8'h06; mem['h0342]=8'h3E; mem['h0343]=8'h20;
    mem['h0344]=8'hCD; mem['h0345]=8'hBC; mem['h0346]=8'h09; mem['h0347]=8'hCD;
    mem['h0348]=8'h02; mem['h0349]=8'h07; mem['h034A]=8'h21; mem['h034B]=8'h00;
    mem['h034C]=8'hFF; mem['h034D]=8'hCD; mem['h034E]=8'h58; mem['h034F]=8'h07;
    mem['h0350]=8'h7E; mem['h0351]=8'hB7; mem['h0352]=8'hC2; mem['h0353]=8'h5D;
    mem['h0354]=8'h03; mem['h0355]=8'hE1; mem['h0356]=8'h23; mem['h0357]=8'h22;
    mem['h0358]=8'h17; mem['h0359]=8'hFF; mem['h035A]=8'hC3; mem['h035B]=8'h32;
    mem['h035C]=8'h03; mem['h035D]=8'hFE; mem['h035E]=8'h2D; mem['h035F]=8'hC2;
    mem['h0360]=8'h6A; mem['h0361]=8'h03; mem['h0362]=8'hE1; mem['h0363]=8'h2B;
    mem['h0364]=8'h22; mem['h0365]=8'h17; mem['h0366]=8'hFF; mem['h0367]=8'hC3;
    mem['h0368]=8'h32; mem['h0369]=8'h03; mem['h036A]=8'hFE; mem['h036B]=8'h2E;
    mem['h036C]=8'hC2; mem['h036D]=8'h76; mem['h036E]=8'h03; mem['h036F]=8'hE1;
    mem['h0370]=8'h22; mem['h0371]=8'h17; mem['h0372]=8'hFF; mem['h0373]=8'hC3;
    mem['h0374]=8'h75; mem['h0375]=8'h01; mem['h0376]=8'hCD; mem['h0377]=8'h69;
    mem['h0378]=8'h07; mem['h0379]=8'h79; mem['h037A]=8'hB7; mem['h037B]=8'hE1;
    mem['h037C]=8'hCA; mem['h037D]=8'hB3; mem['h037E]=8'h01; mem['h037F]=8'h73;
    mem['h0380]=8'h23; mem['h0381]=8'h22; mem['h0382]=8'h17; mem['h0383]=8'hFF;
    mem['h0384]=8'hC3; mem['h0385]=8'h32; mem['h0386]=8'h03; mem['h0387]=8'h23;
    mem['h0388]=8'hCD; mem['h0389]=8'h58; mem['h038A]=8'h07; mem['h038B]=8'hCD;
    mem['h038C]=8'h69; mem['h038D]=8'h07; mem['h038E]=8'hCD; mem['h038F]=8'h58;
    mem['h0390]=8'h07; mem['h0391]=8'h7E; mem['h0392]=8'hB7; mem['h0393]=8'hC2;
    mem['h0394]=8'hB3; mem['h0395]=8'h01; mem['h0396]=8'h79; mem['h0397]=8'hB7;
    mem['h0398]=8'hC2; mem['h0399]=8'h9E; mem['h039A]=8'h03; mem['h039B]=8'h11;
    mem['h039C]=8'h00; mem['h039D]=8'h00; mem['h039E]=8'hCD; mem['h039F]=8'hAD;
    mem['h03A0]=8'h09; mem['h03A1]=8'hCD; mem['h03A2]=8'h60; mem['h03A3]=8'h07;
    mem['h03A4]=8'hFE; mem['h03A5]=8'h53; mem['h03A6]=8'hCA; mem['h03A7]=8'h0F;
    mem['h03A8]=8'h04; mem['h03A9]=8'hFE; mem['h03AA]=8'h3A; mem['h03AB]=8'hCA;
    mem['h03AC]=8'hBE; mem['h03AD]=8'h03; mem['h03AE]=8'hFE; mem['h03AF]=8'h0D;
    mem['h03B0]=8'hCA; mem['h03B1]=8'h9E; mem['h03B2]=8'h03; mem['h03B3]=8'hFE;
    mem['h03B4]=8'h0A; mem['h03B5]=8'hCA; mem['h03B6]=8'h9E; mem['h03B7]=8'h03;
    mem['h03B8]=8'hCD; mem['h03B9]=8'hAD; mem['h03BA]=8'h09; mem['h03BB]=8'hC3;
    mem['h03BC]=8'hAE; mem['h03BD]=8'h03; mem['h03BE]=8'hCD; mem['h03BF]=8'hCD;
    mem['h03C0]=8'h06; mem['h03C1]=8'h4F; mem['h03C2]=8'h47; mem['h03C3]=8'hCD;
    mem['h03C4]=8'hCD; mem['h03C5]=8'h06; mem['h03C6]=8'h67; mem['h03C7]=8'h81;
    mem['h03C8]=8'h4F; mem['h03C9]=8'hCD; mem['h03CA]=8'hCD; mem['h03CB]=8'h06;
    mem['h03CC]=8'h6F; mem['h03CD]=8'h81; mem['h03CE]=8'h4F; mem['h03CF]=8'h19;
    mem['h03D0]=8'hCD; mem['h03D1]=8'hCD; mem['h03D2]=8'h06; mem['h03D3]=8'h32;
    mem['h03D4]=8'h1A; mem['h03D5]=8'hFF; mem['h03D6]=8'h81; mem['h03D7]=8'h4F;
    mem['h03D8]=8'h78; mem['h03D9]=8'hB7; mem['h03DA]=8'hCA; mem['h03DB]=8'hF5;
    mem['h03DC]=8'h03; mem['h03DD]=8'hCD; mem['h03DE]=8'hCD; mem['h03DF]=8'h06;
    mem['h03E0]=8'hF5; mem['h03E1]=8'h81; mem['h03E2]=8'h4F; mem['h03E3]=8'h3A;
    mem['h03E4]=8'h1A; mem['h03E5]=8'hFF; mem['h03E6]=8'hB7; mem['h03E7]=8'hC2;
    mem['h03E8]=8'hF0; mem['h03E9]=8'h03; mem['h03EA]=8'hF1; mem['h03EB]=8'h77;
    mem['h03EC]=8'h23; mem['h03ED]=8'hC3; mem['h03EE]=8'hF1; mem['h03EF]=8'h03;
    mem['h03F0]=8'hF1; mem['h03F1]=8'h05; mem['h03F2]=8'hC2; mem['h03F3]=8'hDD;
    mem['h03F4]=8'h03; mem['h03F5]=8'hCD; mem['h03F6]=8'hCD; mem['h03F7]=8'h06;
    mem['h03F8]=8'h81; mem['h03F9]=8'hC2; mem['h03FA]=8'h06; mem['h03FB]=8'h04;
    mem['h03FC]=8'h3A; mem['h03FD]=8'h1A; mem['h03FE]=8'hFF; mem['h03FF]=8'hB7;
    mem['h0400]=8'hCA; mem['h0401]=8'hB8; mem['h0402]=8'h03; mem['h0403]=8'hC3;
    mem['h0404]=8'h75; mem['h0405]=8'h01; mem['h0406]=8'h21; mem['h0407]=8'h3F;
    mem['h0408]=8'h08; mem['h0409]=8'hCD; mem['h040A]=8'hA7; mem['h040B]=8'h06;
    mem['h040C]=8'hC3; mem['h040D]=8'h75; mem['h040E]=8'h01; mem['h040F]=8'hCD;
    mem['h0410]=8'hAD; mem['h0411]=8'h09; mem['h0412]=8'h32; mem['h0413]=8'h1A;
    mem['h0414]=8'hFF; mem['h0415]=8'hCD; mem['h0416]=8'hCD; mem['h0417]=8'h06;
    mem['h0418]=8'h47; mem['h0419]=8'h4F; mem['h041A]=8'hCD; mem['h041B]=8'hCD;
    mem['h041C]=8'h06; mem['h041D]=8'h67; mem['h041E]=8'h81; mem['h041F]=8'h4F;
    mem['h0420]=8'hCD; mem['h0421]=8'hCD; mem['h0422]=8'h06; mem['h0423]=8'h6F;
    mem['h0424]=8'h81; mem['h0425]=8'h4F; mem['h0426]=8'h19; mem['h0427]=8'h05;
    mem['h0428]=8'h05; mem['h0429]=8'h05; mem['h042A]=8'hCA; mem['h042B]=8'h46;
    mem['h042C]=8'h04; mem['h042D]=8'hCD; mem['h042E]=8'hCD; mem['h042F]=8'h06;
    mem['h0430]=8'hF5; mem['h0431]=8'h81; mem['h0432]=8'h4F; mem['h0433]=8'h3A;
    mem['h0434]=8'h1A; mem['h0435]=8'hFF; mem['h0436]=8'hFE; mem['h0437]=8'h31;
    mem['h0438]=8'hC2; mem['h0439]=8'h41; mem['h043A]=8'h04; mem['h043B]=8'hF1;
    mem['h043C]=8'h77; mem['h043D]=8'h23; mem['h043E]=8'hC3; mem['h043F]=8'h42;
    mem['h0440]=8'h04; mem['h0441]=8'hF1; mem['h0442]=8'h05; mem['h0443]=8'hC2;
    mem['h0444]=8'h2D; mem['h0445]=8'h04; mem['h0446]=8'hCD; mem['h0447]=8'hCD;
    mem['h0448]=8'h06; mem['h0449]=8'h81; mem['h044A]=8'hFE; mem['h044B]=8'hFF;
    mem['h044C]=8'hC2; mem['h044D]=8'h64; mem['h044E]=8'h04; mem['h044F]=8'h3A;
    mem['h0450]=8'h1A; mem['h0451]=8'hFF; mem['h0452]=8'hFE; mem['h0453]=8'h37;
    mem['h0454]=8'hCA; mem['h0455]=8'h75; mem['h0456]=8'h01; mem['h0457]=8'hFE;
    mem['h0458]=8'h38; mem['h0459]=8'hCA; mem['h045A]=8'h75; mem['h045B]=8'h01;
    mem['h045C]=8'hFE; mem['h045D]=8'h39; mem['h045E]=8'hCA; mem['h045F]=8'h75;
    mem['h0460]=8'h01; mem['h0461]=8'hC3; mem['h0462]=8'hB8; mem['h0463]=8'h03;
    mem['h0464]=8'h21; mem['h0465]=8'h5A; mem['h0466]=8'h08; mem['h0467]=8'hCD;
    mem['h0468]=8'hA7; mem['h0469]=8'h06; mem['h046A]=8'hC3; mem['h046B]=8'h75;
    mem['h046C]=8'h01; mem['h046D]=8'h23; mem['h046E]=8'h7E; mem['h046F]=8'hCD;
    mem['h0470]=8'h60; mem['h0471]=8'h07; mem['h0472]=8'hFE; mem['h0473]=8'h49;
    mem['h0474]=8'hCA; mem['h0475]=8'h7C; mem['h0476]=8'h04; mem['h0477]=8'hFE;
    mem['h0478]=8'h53; mem['h0479]=8'hC2; mem['h047A]=8'h80; mem['h047B]=8'h04;
    mem['h047C]=8'h23; mem['h047D]=8'h32; mem['h047E]=8'h19; mem['h047F]=8'hFF;
    mem['h0480]=8'hCD; mem['h0481]=8'h58; mem['h0482]=8'h07; mem['h0483]=8'hCD;
    mem['h0484]=8'h69; mem['h0485]=8'h07; mem['h0486]=8'h79; mem['h0487]=8'hB7;
    mem['h0488]=8'hCA; mem['h0489]=8'hAD; mem['h048A]=8'h04; mem['h048B]=8'hEB;
    mem['h048C]=8'h22; mem['h048D]=8'h28; mem['h048E]=8'hFF; mem['h048F]=8'hEB;
    mem['h0490]=8'hCD; mem['h0491]=8'h58; mem['h0492]=8'h07; mem['h0493]=8'h7E;
    mem['h0494]=8'hFE; mem['h0495]=8'h2C; mem['h0496]=8'hC2; mem['h0497]=8'hAD;
    mem['h0498]=8'h04; mem['h0499]=8'h23; mem['h049A]=8'hCD; mem['h049B]=8'h58;
    mem['h049C]=8'h07; mem['h049D]=8'hCD; mem['h049E]=8'h69; mem['h049F]=8'h07;
    mem['h04A0]=8'h79; mem['h04A1]=8'hB7; mem['h04A2]=8'hCA; mem['h04A3]=8'hAD;
    mem['h04A4]=8'h04; mem['h04A5]=8'hCD; mem['h04A6]=8'h58; mem['h04A7]=8'h07;
    mem['h04A8]=8'h7E; mem['h04A9]=8'hB7; mem['h04AA]=8'hCA; mem['h04AB]=8'hB0;
    mem['h04AC]=8'h04; mem['h04AD]=8'hC3; mem['h04AE]=8'hB3; mem['h04AF]=8'h01;
    mem['h04B0]=8'h2A; mem['h04B1]=8'h28; mem['h04B2]=8'hFF; mem['h04B3]=8'h13;
    mem['h04B4]=8'h7B; mem['h04B5]=8'h95; mem['h04B6]=8'h32; mem['h04B7]=8'h2A;
    mem['h04B8]=8'hFF; mem['h04B9]=8'h7A; mem['h04BA]=8'h9C; mem['h04BB]=8'h32;
    mem['h04BC]=8'h2B; mem['h04BD]=8'hFF; mem['h04BE]=8'hCD; mem['h04BF]=8'hE6;
    mem['h04C0]=8'h04; mem['h04C1]=8'h3A; mem['h04C2]=8'h2A; mem['h04C3]=8'hFF;
    mem['h04C4]=8'h47; mem['h04C5]=8'h3A; mem['h04C6]=8'h2B; mem['h04C7]=8'hFF;
    mem['h04C8]=8'hB0; mem['h04C9]=8'hC2; mem['h04CA]=8'hBE; mem['h04CB]=8'h04;
    mem['h04CC]=8'h3A; mem['h04CD]=8'h19; mem['h04CE]=8'hFF; mem['h04CF]=8'hFE;
    mem['h04D0]=8'h49; mem['h04D1]=8'hCA; mem['h04D2]=8'hDD; mem['h04D3]=8'h04;
    mem['h04D4]=8'h21; mem['h04D5]=8'h67; mem['h04D6]=8'h08; mem['h04D7]=8'hCD;
    mem['h04D8]=8'hA7; mem['h04D9]=8'h06; mem['h04DA]=8'hC3; mem['h04DB]=8'h75;
    mem['h04DC]=8'h01; mem['h04DD]=8'h21; mem['h04DE]=8'h4C; mem['h04DF]=8'h08;
    mem['h04E0]=8'hCD; mem['h04E1]=8'hA7; mem['h04E2]=8'h06; mem['h04E3]=8'hC3;
    mem['h04E4]=8'h75; mem['h04E5]=8'h01; mem['h04E6]=8'h06; mem['h04E7]=8'h10;
    mem['h04E8]=8'h3A; mem['h04E9]=8'h2B; mem['h04EA]=8'hFF; mem['h04EB]=8'hB7;
    mem['h04EC]=8'hC2; mem['h04ED]=8'hF7; mem['h04EE]=8'h04; mem['h04EF]=8'h3A;
    mem['h04F0]=8'h2A; mem['h04F1]=8'hFF; mem['h04F2]=8'hB8; mem['h04F3]=8'hD2;
    mem['h04F4]=8'hF7; mem['h04F5]=8'h04; mem['h04F6]=8'h47; mem['h04F7]=8'h3A;
    mem['h04F8]=8'h2A; mem['h04F9]=8'hFF; mem['h04FA]=8'h90; mem['h04FB]=8'h32;
    mem['h04FC]=8'h2A; mem['h04FD]=8'hFF; mem['h04FE]=8'h3A; mem['h04FF]=8'h2B;
    mem['h0500]=8'hFF; mem['h0501]=8'hDE; mem['h0502]=8'h00; mem['h0503]=8'h32;
    mem['h0504]=8'h2B; mem['h0505]=8'hFF; mem['h0506]=8'h3A; mem['h0507]=8'h19;
    mem['h0508]=8'hFF; mem['h0509]=8'hFE; mem['h050A]=8'h49; mem['h050B]=8'hC2;
    mem['h050C]=8'h41; mem['h050D]=8'h05; mem['h050E]=8'h3E; mem['h050F]=8'h3A;
    mem['h0510]=8'hCD; mem['h0511]=8'hBC; mem['h0512]=8'h09; mem['h0513]=8'h78;
    mem['h0514]=8'hCD; mem['h0515]=8'hB6; mem['h0516]=8'h06; mem['h0517]=8'h78;
    mem['h0518]=8'h4F; mem['h0519]=8'h7C; mem['h051A]=8'hCD; mem['h051B]=8'hB6;
    mem['h051C]=8'h06; mem['h051D]=8'h7C; mem['h051E]=8'h81; mem['h051F]=8'h4F;
    mem['h0520]=8'h7D; mem['h0521]=8'hCD; mem['h0522]=8'hB6; mem['h0523]=8'h06;
    mem['h0524]=8'h7D; mem['h0525]=8'h81; mem['h0526]=8'h4F; mem['h0527]=8'hAF;
    mem['h0528]=8'hCD; mem['h0529]=8'hB6; mem['h052A]=8'h06; mem['h052B]=8'h7E;
    mem['h052C]=8'hF5; mem['h052D]=8'hCD; mem['h052E]=8'hB6; mem['h052F]=8'h06;
    mem['h0530]=8'hF1; mem['h0531]=8'h81; mem['h0532]=8'h4F; mem['h0533]=8'h23;
    mem['h0534]=8'h05; mem['h0535]=8'hC2; mem['h0536]=8'h2B; mem['h0537]=8'h05;
    mem['h0538]=8'h79; mem['h0539]=8'h2F; mem['h053A]=8'h3C; mem['h053B]=8'hCD;
    mem['h053C]=8'hB6; mem['h053D]=8'h06; mem['h053E]=8'hC3; mem['h053F]=8'hF8;
    mem['h0540]=8'h06; mem['h0541]=8'h3E; mem['h0542]=8'h53; mem['h0543]=8'hCD;
    mem['h0544]=8'hBC; mem['h0545]=8'h09; mem['h0546]=8'h3E; mem['h0547]=8'h31;
    mem['h0548]=8'hCD; mem['h0549]=8'hBC; mem['h054A]=8'h09; mem['h054B]=8'h78;
    mem['h054C]=8'hC6; mem['h054D]=8'h03; mem['h054E]=8'h4F; mem['h054F]=8'hCD;
    mem['h0550]=8'hB6; mem['h0551]=8'h06; mem['h0552]=8'h7C; mem['h0553]=8'hCD;
    mem['h0554]=8'hB6; mem['h0555]=8'h06; mem['h0556]=8'h7C; mem['h0557]=8'h81;
    mem['h0558]=8'h4F; mem['h0559]=8'h7D; mem['h055A]=8'hCD; mem['h055B]=8'hB6;
    mem['h055C]=8'h06; mem['h055D]=8'h7D; mem['h055E]=8'h81; mem['h055F]=8'h4F;
    mem['h0560]=8'h7E; mem['h0561]=8'hF5; mem['h0562]=8'hCD; mem['h0563]=8'hB6;
    mem['h0564]=8'h06; mem['h0565]=8'hF1; mem['h0566]=8'h81; mem['h0567]=8'h4F;
    mem['h0568]=8'h23; mem['h0569]=8'h05; mem['h056A]=8'hC2; mem['h056B]=8'h60;
    mem['h056C]=8'h05; mem['h056D]=8'h79; mem['h056E]=8'h2F; mem['h056F]=8'hCD;
    mem['h0570]=8'hB6; mem['h0571]=8'h06; mem['h0572]=8'hC3; mem['h0573]=8'hF8;
    mem['h0574]=8'h06; mem['h0575]=8'h23; mem['h0576]=8'hCD; mem['h0577]=8'h58;
    mem['h0578]=8'h07; mem['h0579]=8'hCD; mem['h057A]=8'h69; mem['h057B]=8'h07;
    mem['h057C]=8'h79; mem['h057D]=8'hB7; mem['h057E]=8'hCA; mem['h057F]=8'hB3;
    mem['h0580]=8'h01; mem['h0581]=8'hCD; mem['h0582]=8'h58; mem['h0583]=8'h07;
    mem['h0584]=8'h7E; mem['h0585]=8'hB7; mem['h0586]=8'hC2; mem['h0587]=8'hB3;
    mem['h0588]=8'h01; mem['h0589]=8'h21; mem['h058A]=8'h00; mem['h058B]=8'hFF;
    mem['h058C]=8'h36; mem['h058D]=8'hDB; mem['h058E]=8'h23; mem['h058F]=8'h73;
    mem['h0590]=8'h23; mem['h0591]=8'h36; mem['h0592]=8'hC9; mem['h0593]=8'hCD;
    mem['h0594]=8'h00; mem['h0595]=8'hFF; mem['h0596]=8'hCD; mem['h0597]=8'hB6;
    mem['h0598]=8'h06; mem['h0599]=8'hCD; mem['h059A]=8'hF8; mem['h059B]=8'h06;
    mem['h059C]=8'hC3; mem['h059D]=8'h75; mem['h059E]=8'h01; mem['h059F]=8'h23;
    mem['h05A0]=8'hCD; mem['h05A1]=8'h58; mem['h05A2]=8'h07; mem['h05A3]=8'hCD;
    mem['h05A4]=8'h69; mem['h05A5]=8'h07; mem['h05A6]=8'h79; mem['h05A7]=8'hB7;
    mem['h05A8]=8'hCA; mem['h05A9]=8'hB3; mem['h05AA]=8'h01; mem['h05AB]=8'h43;
    mem['h05AC]=8'hCD; mem['h05AD]=8'h58; mem['h05AE]=8'h07; mem['h05AF]=8'h7E;
    mem['h05B0]=8'hFE; mem['h05B1]=8'h2C; mem['h05B2]=8'hC2; mem['h05B3]=8'hB3;
    mem['h05B4]=8'h01; mem['h05B5]=8'h23; mem['h05B6]=8'hCD; mem['h05B7]=8'h58;
    mem['h05B8]=8'h07; mem['h05B9]=8'hCD; mem['h05BA]=8'h69; mem['h05BB]=8'h07;
    mem['h05BC]=8'h79; mem['h05BD]=8'hB7; mem['h05BE]=8'hCA; mem['h05BF]=8'hB3;
    mem['h05C0]=8'h01; mem['h05C1]=8'hCD; mem['h05C2]=8'h58; mem['h05C3]=8'h07;
    mem['h05C4]=8'h7E; mem['h05C5]=8'hB7; mem['h05C6]=8'hC2; mem['h05C7]=8'hB3;
    mem['h05C8]=8'h01; mem['h05C9]=8'h21; mem['h05CA]=8'h00; mem['h05CB]=8'hFF;
    mem['h05CC]=8'h36; mem['h05CD]=8'hD3; mem['h05CE]=8'h23; mem['h05CF]=8'h70;
    mem['h05D0]=8'h23; mem['h05D1]=8'h36; mem['h05D2]=8'hC9; mem['h05D3]=8'h7B;
    mem['h05D4]=8'hCD; mem['h05D5]=8'h00; mem['h05D6]=8'hFF; mem['h05D7]=8'hC3;
    mem['h05D8]=8'h75; mem['h05D9]=8'h01; mem['h05DA]=8'h23; mem['h05DB]=8'hCD;
    mem['h05DC]=8'h58; mem['h05DD]=8'h07; mem['h05DE]=8'hCD; mem['h05DF]=8'h60;
    mem['h05E0]=8'h07; mem['h05E1]=8'hB7; mem['h05E2]=8'hC2; mem['h05E3]=8'hEB;
    mem['h05E4]=8'h05; mem['h05E5]=8'hCD; mem['h05E6]=8'h74; mem['h05E7]=8'h06;
    mem['h05E8]=8'hC3; mem['h05E9]=8'h75; mem['h05EA]=8'h01; mem['h05EB]=8'hEB;
    mem['h05EC]=8'h21; mem['h05ED]=8'hE5; mem['h05EE]=8'h08; mem['h05EF]=8'hBE;
    mem['h05F0]=8'hCA; mem['h05F1]=8'h02; mem['h05F2]=8'h06; mem['h05F3]=8'h4F;
    mem['h05F4]=8'h23; mem['h05F5]=8'h7E; mem['h05F6]=8'hB7; mem['h05F7]=8'hCA;
    mem['h05F8]=8'h71; mem['h05F9]=8'h06; mem['h05FA]=8'h79; mem['h05FB]=8'h01;
    mem['h05FC]=8'h05; mem['h05FD]=8'h00; mem['h05FE]=8'h09; mem['h05FF]=8'hC3;
    mem['h0600]=8'hEF; mem['h0601]=8'h05; mem['h0602]=8'h23; mem['h0603]=8'h7E;
    mem['h0604]=8'hFE; mem['h0605]=8'h0F; mem['h0606]=8'hC2; mem['h0607]=8'h16;
    mem['h0608]=8'h06; mem['h0609]=8'h23; mem['h060A]=8'h4E; mem['h060B]=8'h23;
    mem['h060C]=8'h66; mem['h060D]=8'h69; mem['h060E]=8'h13; mem['h060F]=8'h1A;
    mem['h0610]=8'hCD; mem['h0611]=8'h60; mem['h0612]=8'h07; mem['h0613]=8'hC3;
    mem['h0614]=8'hEF; mem['h0615]=8'h05; mem['h0616]=8'hB7; mem['h0617]=8'hCA;
    mem['h0618]=8'h71; mem['h0619]=8'h06; mem['h061A]=8'h4E; mem['h061B]=8'h23;
    mem['h061C]=8'h5E; mem['h061D]=8'h23; mem['h061E]=8'h56; mem['h061F]=8'hD5;
    mem['h0620]=8'h23; mem['h0621]=8'h7E; mem['h0622]=8'h23; mem['h0623]=8'h66;
    mem['h0624]=8'h6F; mem['h0625]=8'hCD; mem['h0626]=8'hA7; mem['h0627]=8'h06;
    mem['h0628]=8'h3E; mem['h0629]=8'h3D; mem['h062A]=8'hCD; mem['h062B]=8'hBC;
    mem['h062C]=8'h09; mem['h062D]=8'h79; mem['h062E]=8'hE6; mem['h062F]=8'h07;
    mem['h0630]=8'hFE; mem['h0631]=8'h01; mem['h0632]=8'hC2; mem['h0633]=8'h3E;
    mem['h0634]=8'h06; mem['h0635]=8'hE1; mem['h0636]=8'h7E; mem['h0637]=8'hE5;
    mem['h0638]=8'hCD; mem['h0639]=8'hB6; mem['h063A]=8'h06; mem['h063B]=8'hC3;
    mem['h063C]=8'h47; mem['h063D]=8'h06; mem['h063E]=8'hE1; mem['h063F]=8'hE5;
    mem['h0640]=8'h5E; mem['h0641]=8'h23; mem['h0642]=8'h56; mem['h0643]=8'hEB;
    mem['h0644]=8'hCD; mem['h0645]=8'hB1; mem['h0646]=8'h06; mem['h0647]=8'h3E;
    mem['h0648]=8'h20; mem['h0649]=8'hCD; mem['h064A]=8'hBC; mem['h064B]=8'h09;
    mem['h064C]=8'hC5; mem['h064D]=8'hCD; mem['h064E]=8'h02; mem['h064F]=8'h07;
    mem['h0650]=8'h21; mem['h0651]=8'h00; mem['h0652]=8'hFF; mem['h0653]=8'hCD;
    mem['h0654]=8'h58; mem['h0655]=8'h07; mem['h0656]=8'hCD; mem['h0657]=8'h69;
    mem['h0658]=8'h07; mem['h0659]=8'h79; mem['h065A]=8'hB7; mem['h065B]=8'hCA;
    mem['h065C]=8'h6E; mem['h065D]=8'h06; mem['h065E]=8'hC1; mem['h065F]=8'h79;
    mem['h0660]=8'hFE; mem['h0661]=8'h01; mem['h0662]=8'hC2; mem['h0663]=8'h6A;
    mem['h0664]=8'h06; mem['h0665]=8'hE1; mem['h0666]=8'h73; mem['h0667]=8'hC3;
    mem['h0668]=8'h6E; mem['h0669]=8'h06; mem['h066A]=8'hE1; mem['h066B]=8'h73;
    mem['h066C]=8'h23; mem['h066D]=8'h72; mem['h066E]=8'hC3; mem['h066F]=8'h75;
    mem['h0670]=8'h01; mem['h0671]=8'hC3; mem['h0672]=8'hB3; mem['h0673]=8'h01;
    mem['h0674]=8'h21; mem['h0675]=8'h9D; mem['h0676]=8'h08; mem['h0677]=8'h5E;
    mem['h0678]=8'h23; mem['h0679]=8'h56; mem['h067A]=8'h23; mem['h067B]=8'h7A;
    mem['h067C]=8'hB3; mem['h067D]=8'hCA; mem['h067E]=8'hF8; mem['h067F]=8'h06;
    mem['h0680]=8'hEB; mem['h0681]=8'hCD; mem['h0682]=8'hA7; mem['h0683]=8'h06;
    mem['h0684]=8'hEB; mem['h0685]=8'h5E; mem['h0686]=8'h23; mem['h0687]=8'h56;
    mem['h0688]=8'h23; mem['h0689]=8'h7E; mem['h068A]=8'h23; mem['h068B]=8'hEB;
    mem['h068C]=8'hFE; mem['h068D]=8'h01; mem['h068E]=8'hC2; mem['h068F]=8'h99;
    mem['h0690]=8'h06; mem['h0691]=8'h7E; mem['h0692]=8'hCD; mem['h0693]=8'hB6;
    mem['h0694]=8'h06; mem['h0695]=8'hEB; mem['h0696]=8'hC3; mem['h0697]=8'h77;
    mem['h0698]=8'h06; mem['h0699]=8'h23; mem['h069A]=8'h7E; mem['h069B]=8'hCD;
    mem['h069C]=8'hB6; mem['h069D]=8'h06; mem['h069E]=8'h2B; mem['h069F]=8'h7E;
    mem['h06A0]=8'hCD; mem['h06A1]=8'hB6; mem['h06A2]=8'h06; mem['h06A3]=8'hEB;
    mem['h06A4]=8'hC3; mem['h06A5]=8'h77; mem['h06A6]=8'h06; mem['h06A7]=8'h7E;
    mem['h06A8]=8'hA7; mem['h06A9]=8'hC8; mem['h06AA]=8'hCD; mem['h06AB]=8'hBC;
    mem['h06AC]=8'h09; mem['h06AD]=8'h23; mem['h06AE]=8'hC3; mem['h06AF]=8'hA7;
    mem['h06B0]=8'h06; mem['h06B1]=8'h7C; mem['h06B2]=8'hCD; mem['h06B3]=8'hB6;
    mem['h06B4]=8'h06; mem['h06B5]=8'h7D; mem['h06B6]=8'hF5; mem['h06B7]=8'h1F;
    mem['h06B8]=8'h1F; mem['h06B9]=8'h1F; mem['h06BA]=8'h1F; mem['h06BB]=8'hCD;
    mem['h06BC]=8'hBF; mem['h06BD]=8'h06; mem['h06BE]=8'hF1; mem['h06BF]=8'hE6;
    mem['h06C0]=8'h0F; mem['h06C1]=8'hC6; mem['h06C2]=8'h30; mem['h06C3]=8'hFE;
    mem['h06C4]=8'h3A; mem['h06C5]=8'hDA; mem['h06C6]=8'hBC; mem['h06C7]=8'h09;
    mem['h06C8]=8'hC6; mem['h06C9]=8'h07; mem['h06CA]=8'hC3; mem['h06CB]=8'hBC;
    mem['h06CC]=8'h09; mem['h06CD]=8'hAF; mem['h06CE]=8'hCD; mem['h06CF]=8'hD5;
    mem['h06D0]=8'h06; mem['h06D1]=8'h07; mem['h06D2]=8'h07; mem['h06D3]=8'h07;
    mem['h06D4]=8'h07; mem['h06D5]=8'hC5; mem['h06D6]=8'h4F; mem['h06D7]=8'hCD;
    mem['h06D8]=8'hAD; mem['h06D9]=8'h09; mem['h06DA]=8'hCD; mem['h06DB]=8'h60;
    mem['h06DC]=8'h07; mem['h06DD]=8'hFE; mem['h06DE]=8'h30; mem['h06DF]=8'hDA;
    mem['h06E0]=8'hF6; mem['h06E1]=8'h06; mem['h06E2]=8'hFE; mem['h06E3]=8'h3A;
    mem['h06E4]=8'hDA; mem['h06E5]=8'hF3; mem['h06E6]=8'h06; mem['h06E7]=8'hFE;
    mem['h06E8]=8'h41; mem['h06E9]=8'hDA; mem['h06EA]=8'hF6; mem['h06EB]=8'h06;
    mem['h06EC]=8'hFE; mem['h06ED]=8'h47; mem['h06EE]=8'hD2; mem['h06EF]=8'hF6;
    mem['h06F0]=8'h06; mem['h06F1]=8'hD6; mem['h06F2]=8'h07; mem['h06F3]=8'hD6;
    mem['h06F4]=8'h30; mem['h06F5]=8'hB1; mem['h06F6]=8'hC1; mem['h06F7]=8'hC9;
    mem['h06F8]=8'h3E; mem['h06F9]=8'h0D; mem['h06FA]=8'hCD; mem['h06FB]=8'hBC;
    mem['h06FC]=8'h09; mem['h06FD]=8'h3E; mem['h06FE]=8'h0A; mem['h06FF]=8'hC3;
    mem['h0700]=8'hBC; mem['h0701]=8'h09; mem['h0702]=8'h21; mem['h0703]=8'h00;
    mem['h0704]=8'hFF; mem['h0705]=8'h06; mem['h0706]=8'h00; mem['h0707]=8'hCD;
    mem['h0708]=8'hAD; mem['h0709]=8'h09; mem['h070A]=8'hFE; mem['h070B]=8'h0D;
    mem['h070C]=8'hCA; mem['h070D]=8'h52; mem['h070E]=8'h07; mem['h070F]=8'hFE;
    mem['h0710]=8'h0A; mem['h0711]=8'hCA; mem['h0712]=8'h52; mem['h0713]=8'h07;
    mem['h0714]=8'hFE; mem['h0715]=8'h08; mem['h0716]=8'hCA; mem['h0717]=8'h39;
    mem['h0718]=8'h07; mem['h0719]=8'hFE; mem['h071A]=8'h7F; mem['h071B]=8'hCA;
    mem['h071C]=8'h39; mem['h071D]=8'h07; mem['h071E]=8'hFE; mem['h071F]=8'h20;
    mem['h0720]=8'hDA; mem['h0721]=8'h07; mem['h0722]=8'h07; mem['h0723]=8'hFE;
    mem['h0724]=8'h80; mem['h0725]=8'hD2; mem['h0726]=8'h07; mem['h0727]=8'h07;
    mem['h0728]=8'h4F; mem['h0729]=8'h78; mem['h072A]=8'hFE; mem['h072B]=8'h0F;
    mem['h072C]=8'hD2; mem['h072D]=8'h07; mem['h072E]=8'h07; mem['h072F]=8'h04;
    mem['h0730]=8'h79; mem['h0731]=8'hCD; mem['h0732]=8'hBC; mem['h0733]=8'h09;
    mem['h0734]=8'h77; mem['h0735]=8'h23; mem['h0736]=8'hC3; mem['h0737]=8'h07;
    mem['h0738]=8'h07; mem['h0739]=8'h78; mem['h073A]=8'hA7; mem['h073B]=8'hCA;
    mem['h073C]=8'h07; mem['h073D]=8'h07; mem['h073E]=8'h05; mem['h073F]=8'h2B;
    mem['h0740]=8'h3E; mem['h0741]=8'h08; mem['h0742]=8'hCD; mem['h0743]=8'hBC;
    mem['h0744]=8'h09; mem['h0745]=8'h3E; mem['h0746]=8'h20; mem['h0747]=8'hCD;
    mem['h0748]=8'hBC; mem['h0749]=8'h09; mem['h074A]=8'h3E; mem['h074B]=8'h08;
    mem['h074C]=8'hCD; mem['h074D]=8'hBC; mem['h074E]=8'h09; mem['h074F]=8'hC3;
    mem['h0750]=8'h07; mem['h0751]=8'h07; mem['h0752]=8'hCD; mem['h0753]=8'hF8;
    mem['h0754]=8'h06; mem['h0755]=8'h36; mem['h0756]=8'h00; mem['h0757]=8'hC9;
    mem['h0758]=8'h7E; mem['h0759]=8'hFE; mem['h075A]=8'h20; mem['h075B]=8'hC0;
    mem['h075C]=8'h23; mem['h075D]=8'hC3; mem['h075E]=8'h58; mem['h075F]=8'h07;
    mem['h0760]=8'hFE; mem['h0761]=8'h61; mem['h0762]=8'hD8; mem['h0763]=8'hFE;
    mem['h0764]=8'h7B; mem['h0765]=8'hD0; mem['h0766]=8'hC6; mem['h0767]=8'hE0;
    mem['h0768]=8'hC9; mem['h0769]=8'h0E; mem['h076A]=8'h00; mem['h076B]=8'h11;
    mem['h076C]=8'h00; mem['h076D]=8'h00; mem['h076E]=8'h7E; mem['h076F]=8'hCD;
    mem['h0770]=8'h60; mem['h0771]=8'h07; mem['h0772]=8'hFE; mem['h0773]=8'h30;
    mem['h0774]=8'hDA; mem['h0775]=8'hB5; mem['h0776]=8'h07; mem['h0777]=8'hFE;
    mem['h0778]=8'h3A; mem['h0779]=8'hDA; mem['h077A]=8'h88; mem['h077B]=8'h07;
    mem['h077C]=8'hFE; mem['h077D]=8'h41; mem['h077E]=8'hDA; mem['h077F]=8'hB5;
    mem['h0780]=8'h07; mem['h0781]=8'hFE; mem['h0782]=8'h47; mem['h0783]=8'hD2;
    mem['h0784]=8'hB5; mem['h0785]=8'h07; mem['h0786]=8'hD6; mem['h0787]=8'h07;
    mem['h0788]=8'hD6; mem['h0789]=8'h30; mem['h078A]=8'h17; mem['h078B]=8'h17;
    mem['h078C]=8'h17; mem['h078D]=8'h17; mem['h078E]=8'h17; mem['h078F]=8'hF5;
    mem['h0790]=8'h7B; mem['h0791]=8'h17; mem['h0792]=8'h5F; mem['h0793]=8'h7A;
    mem['h0794]=8'h17; mem['h0795]=8'h57; mem['h0796]=8'hF1; mem['h0797]=8'h17;
    mem['h0798]=8'hF5; mem['h0799]=8'h7B; mem['h079A]=8'h17; mem['h079B]=8'h5F;
    mem['h079C]=8'h7A; mem['h079D]=8'h17; mem['h079E]=8'h57; mem['h079F]=8'hF1;
    mem['h07A0]=8'h17; mem['h07A1]=8'hF5; mem['h07A2]=8'h7B; mem['h07A3]=8'h17;
    mem['h07A4]=8'h5F; mem['h07A5]=8'h7A; mem['h07A6]=8'h17; mem['h07A7]=8'h57;
    mem['h07A8]=8'hF1; mem['h07A9]=8'h17; mem['h07AA]=8'h7B; mem['h07AB]=8'h17;
    mem['h07AC]=8'h5F; mem['h07AD]=8'h7A; mem['h07AE]=8'h17; mem['h07AF]=8'h57;
    mem['h07B0]=8'h23; mem['h07B1]=8'h0C; mem['h07B2]=8'hC3; mem['h07B3]=8'h6E;
    mem['h07B4]=8'h07; mem['h07B5]=8'hC9; mem['h07B6]=8'hE5; mem['h07B7]=8'hC5;
    mem['h07B8]=8'h21; mem['h07B9]=8'hC6; mem['h07BA]=8'h07; mem['h07BB]=8'h06;
    mem['h07BC]=8'h00; mem['h07BD]=8'h09; mem['h07BE]=8'h09; mem['h07BF]=8'h46;
    mem['h07C0]=8'h23; mem['h07C1]=8'h66; mem['h07C2]=8'h68; mem['h07C3]=8'hC1;
    mem['h07C4]=8'hE3; mem['h07C5]=8'hC9; mem['h07C6]=8'hD4; mem['h07C7]=8'h07;
    mem['h07C8]=8'hD9; mem['h07C9]=8'h07; mem['h07CA]=8'hBC; mem['h07CB]=8'h09;
    mem['h07CC]=8'hA7; mem['h07CD]=8'h06; mem['h07CE]=8'hAD; mem['h07CF]=8'h09;
    mem['h07D0]=8'hB7; mem['h07D1]=8'h09; mem['h07D2]=8'hDD; mem['h07D3]=8'h07;
    mem['h07D4]=8'hE1; mem['h07D5]=8'hF3; mem['h07D6]=8'hF2; mem['h07D7]=8'h00;
    mem['h07D8]=8'h01; mem['h07D9]=8'hE1; mem['h07DA]=8'hF2; mem['h07DB]=8'h75;
    mem['h07DC]=8'h01; mem['h07DD]=8'h3A; mem['h07DE]=8'h1B; mem['h07DF]=8'hFF;
    mem['h07E0]=8'hC9; mem['h07E1]=8'hF5; mem['h07E2]=8'h22; mem['h07E3]=8'h21;
    mem['h07E4]=8'hFF; mem['h07E5]=8'h21; mem['h07E6]=8'h1D; mem['h07E7]=8'hFF;
    mem['h07E8]=8'h71; mem['h07E9]=8'h23; mem['h07EA]=8'h70; mem['h07EB]=8'h23;
    mem['h07EC]=8'h73; mem['h07ED]=8'h23; mem['h07EE]=8'h72; mem['h07EF]=8'hC1;
    mem['h07F0]=8'h78; mem['h07F1]=8'h32; mem['h07F2]=8'h1C; mem['h07F3]=8'hFF;
    mem['h07F4]=8'h79; mem['h07F5]=8'h32; mem['h07F6]=8'h27; mem['h07F7]=8'hFF;
    mem['h07F8]=8'hE1; mem['h07F9]=8'h2B; mem['h07FA]=8'h22; mem['h07FB]=8'h25;
    mem['h07FC]=8'hFF; mem['h07FD]=8'h21; mem['h07FE]=8'h00; mem['h07FF]=8'h00;
    mem['h0800]=8'h39; mem['h0801]=8'h22; mem['h0802]=8'h23; mem['h0803]=8'hFF;
    mem['h0804]=8'h21; mem['h0805]=8'h95; mem['h0806]=8'h08; mem['h0807]=8'hCD;
    mem['h0808]=8'hA7; mem['h0809]=8'h06; mem['h080A]=8'hCD; mem['h080B]=8'h74;
    mem['h080C]=8'h06; mem['h080D]=8'hC3; mem['h080E]=8'h75; mem['h080F]=8'h01;
    mem['h0810]=8'hFB; mem['h0811]=8'hC9; mem['h0812]=8'h0D; mem['h0813]=8'h0A;
    mem['h0814]=8'h55; mem['h0815]=8'h6E; mem['h0816]=8'h69; mem['h0817]=8'h76;
    mem['h0818]=8'h65; mem['h0819]=8'h72; mem['h081A]=8'h73; mem['h081B]=8'h61;
    mem['h081C]=8'h6C; mem['h081D]=8'h20; mem['h081E]=8'h4D; mem['h081F]=8'h6F;
    mem['h0820]=8'h6E; mem['h0821]=8'h69; mem['h0822]=8'h74; mem['h0823]=8'h6F;
    mem['h0824]=8'h72; mem['h0825]=8'h20; mem['h0826]=8'h38; mem['h0827]=8'h30;
    mem['h0828]=8'h38; mem['h0829]=8'h30; mem['h082A]=8'h0D; mem['h082B]=8'h0A;
    mem['h082C]=8'h00; mem['h082D]=8'h5D; mem['h082E]=8'h20; mem['h082F]=8'h00;
    mem['h0830]=8'h45; mem['h0831]=8'h72; mem['h0832]=8'h72; mem['h0833]=8'h6F;
    mem['h0834]=8'h72; mem['h0835]=8'h0D; mem['h0836]=8'h0A; mem['h0837]=8'h00;
    mem['h0838]=8'h20; mem['h0839]=8'h3A; mem['h083A]=8'h00; mem['h083B]=8'h20;
    mem['h083C]=8'h3A; mem['h083D]=8'h20; mem['h083E]=8'h00; mem['h083F]=8'h45;
    mem['h0840]=8'h72; mem['h0841]=8'h72; mem['h0842]=8'h6F; mem['h0843]=8'h72;
    mem['h0844]=8'h20; mem['h0845]=8'h69; mem['h0846]=8'h68; mem['h0847]=8'h65;
    mem['h0848]=8'h78; mem['h0849]=8'h0D; mem['h084A]=8'h0A; mem['h084B]=8'h00;
    mem['h084C]=8'h3A; mem['h084D]=8'h30; mem['h084E]=8'h30; mem['h084F]=8'h30;
    mem['h0850]=8'h30; mem['h0851]=8'h30; mem['h0852]=8'h30; mem['h0853]=8'h30;
    mem['h0854]=8'h31; mem['h0855]=8'h46; mem['h0856]=8'h46; mem['h0857]=8'h0D;
    mem['h0858]=8'h0A; mem['h0859]=8'h00; mem['h085A]=8'h45; mem['h085B]=8'h72;
    mem['h085C]=8'h72; mem['h085D]=8'h6F; mem['h085E]=8'h72; mem['h085F]=8'h20;
    mem['h0860]=8'h73; mem['h0861]=8'h72; mem['h0862]=8'h65; mem['h0863]=8'h63;
    mem['h0864]=8'h0D; mem['h0865]=8'h0A; mem['h0866]=8'h00; mem['h0867]=8'h53;
    mem['h0868]=8'h39; mem['h0869]=8'h30; mem['h086A]=8'h33; mem['h086B]=8'h30;
    mem['h086C]=8'h30; mem['h086D]=8'h30; mem['h086E]=8'h30; mem['h086F]=8'h46;
    mem['h0870]=8'h43; mem['h0871]=8'h0D; mem['h0872]=8'h0A; mem['h0873]=8'h00;
    mem['h0874]=8'h69; mem['h0875]=8'h38; mem['h0876]=8'h30; mem['h0877]=8'h38;
    mem['h0878]=8'h30; mem['h0879]=8'h0D; mem['h087A]=8'h0A; mem['h087B]=8'h00;
    mem['h087C]=8'h75; mem['h087D]=8'h50; mem['h087E]=8'h44; mem['h087F]=8'h38;
    mem['h0880]=8'h30; mem['h0881]=8'h38; mem['h0882]=8'h30; mem['h0883]=8'h41;
    mem['h0884]=8'h0D; mem['h0885]=8'h0A; mem['h0886]=8'h00; mem['h0887]=8'h69;
    mem['h0888]=8'h38; mem['h0889]=8'h30; mem['h088A]=8'h38; mem['h088B]=8'h35;
    mem['h088C]=8'h0D; mem['h088D]=8'h0A; mem['h088E]=8'h00; mem['h088F]=8'h5A;
    mem['h0890]=8'h38; mem['h0891]=8'h30; mem['h0892]=8'h0D; mem['h0893]=8'h0A;
    mem['h0894]=8'h00; mem['h0895]=8'h52; mem['h0896]=8'h53; mem['h0897]=8'h54;
    mem['h0898]=8'h20; mem['h0899]=8'h37; mem['h089A]=8'h0D; mem['h089B]=8'h0A;
    mem['h089C]=8'h00; mem['h089D]=8'hC5; mem['h089E]=8'h08; mem['h089F]=8'h1C;
    mem['h08A0]=8'hFF; mem['h08A1]=8'h01; mem['h08A2]=8'hC8; mem['h08A3]=8'h08;
    mem['h08A4]=8'h1D; mem['h08A5]=8'hFF; mem['h08A6]=8'h02; mem['h08A7]=8'hCD;
    mem['h08A8]=8'h08; mem['h08A9]=8'h1F; mem['h08AA]=8'hFF; mem['h08AB]=8'h02;
    mem['h08AC]=8'hD2; mem['h08AD]=8'h08; mem['h08AE]=8'h21; mem['h08AF]=8'hFF;
    mem['h08B0]=8'h02; mem['h08B1]=8'hD7; mem['h08B2]=8'h08; mem['h08B3]=8'h23;
    mem['h08B4]=8'hFF; mem['h08B5]=8'h02; mem['h08B6]=8'hDC; mem['h08B7]=8'h08;
    mem['h08B8]=8'h25; mem['h08B9]=8'hFF; mem['h08BA]=8'h02; mem['h08BB]=8'hE1;
    mem['h08BC]=8'h08; mem['h08BD]=8'h27; mem['h08BE]=8'hFF; mem['h08BF]=8'h01;
    mem['h08C0]=8'h00; mem['h08C1]=8'h00; mem['h08C2]=8'h00; mem['h08C3]=8'h00;
    mem['h08C4]=8'h00; mem['h08C5]=8'h41; mem['h08C6]=8'h3D; mem['h08C7]=8'h00;
    mem['h08C8]=8'h20; mem['h08C9]=8'h42; mem['h08CA]=8'h43; mem['h08CB]=8'h3D;
    mem['h08CC]=8'h00; mem['h08CD]=8'h20; mem['h08CE]=8'h44; mem['h08CF]=8'h45;
    mem['h08D0]=8'h3D; mem['h08D1]=8'h00; mem['h08D2]=8'h20; mem['h08D3]=8'h48;
    mem['h08D4]=8'h4C; mem['h08D5]=8'h3D; mem['h08D6]=8'h00; mem['h08D7]=8'h20;
    mem['h08D8]=8'h53; mem['h08D9]=8'h50; mem['h08DA]=8'h3D; mem['h08DB]=8'h00;
    mem['h08DC]=8'h20; mem['h08DD]=8'h50; mem['h08DE]=8'h43; mem['h08DF]=8'h3D;
    mem['h08E0]=8'h00; mem['h08E1]=8'h20; mem['h08E2]=8'h46; mem['h08E3]=8'h3D;
    mem['h08E4]=8'h00; mem['h08E5]=8'h41; mem['h08E6]=8'h01; mem['h08E7]=8'h1C;
    mem['h08E8]=8'hFF; mem['h08E9]=8'h75; mem['h08EA]=8'h09; mem['h08EB]=8'h42;
    mem['h08EC]=8'h0F; mem['h08ED]=8'h27; mem['h08EE]=8'h09; mem['h08EF]=8'h00;
    mem['h08F0]=8'h00; mem['h08F1]=8'h43; mem['h08F2]=8'h01; mem['h08F3]=8'h1D;
    mem['h08F4]=8'hFF; mem['h08F5]=8'h7C; mem['h08F6]=8'h09; mem['h08F7]=8'h44;
    mem['h08F8]=8'h0F; mem['h08F9]=8'h39; mem['h08FA]=8'h09; mem['h08FB]=8'h00;
    mem['h08FC]=8'h00; mem['h08FD]=8'h45; mem['h08FE]=8'h01; mem['h08FF]=8'h1F;
    mem['h0900]=8'hFF; mem['h0901]=8'h83; mem['h0902]=8'h09; mem['h0903]=8'h46;
    mem['h0904]=8'h01; mem['h0905]=8'h27; mem['h0906]=8'hFF; mem['h0907]=8'h85;
    mem['h0908]=8'h09; mem['h0909]=8'h48; mem['h090A]=8'h0F; mem['h090B]=8'h4B;
    mem['h090C]=8'h09; mem['h090D]=8'h00; mem['h090E]=8'h00; mem['h090F]=8'h4C;
    mem['h0910]=8'h01; mem['h0911]=8'h21; mem['h0912]=8'hFF; mem['h0913]=8'h8C;
    mem['h0914]=8'h09; mem['h0915]=8'h50; mem['h0916]=8'h0F; mem['h0917]=8'h5D;
    mem['h0918]=8'h09; mem['h0919]=8'h00; mem['h091A]=8'h00; mem['h091B]=8'h53;
    mem['h091C]=8'h0F; mem['h091D]=8'h69; mem['h091E]=8'h09; mem['h091F]=8'h00;
    mem['h0920]=8'h00; mem['h0921]=8'h00; mem['h0922]=8'h00; mem['h0923]=8'h00;
    mem['h0924]=8'h00; mem['h0925]=8'h00; mem['h0926]=8'h00; mem['h0927]=8'h00;
    mem['h0928]=8'h01; mem['h0929]=8'h1E; mem['h092A]=8'hFF; mem['h092B]=8'h7A;
    mem['h092C]=8'h09; mem['h092D]=8'h43; mem['h092E]=8'h02; mem['h092F]=8'h1D;
    mem['h0930]=8'hFF; mem['h0931]=8'h77; mem['h0932]=8'h09; mem['h0933]=8'h00;
    mem['h0934]=8'h00; mem['h0935]=8'h00; mem['h0936]=8'h00; mem['h0937]=8'h00;
    mem['h0938]=8'h00; mem['h0939]=8'h00; mem['h093A]=8'h01; mem['h093B]=8'h20;
    mem['h093C]=8'hFF; mem['h093D]=8'h81; mem['h093E]=8'h09; mem['h093F]=8'h45;
    mem['h0940]=8'h02; mem['h0941]=8'h1F; mem['h0942]=8'hFF; mem['h0943]=8'h7E;
    mem['h0944]=8'h09; mem['h0945]=8'h00; mem['h0946]=8'h00; mem['h0947]=8'h00;
    mem['h0948]=8'h00; mem['h0949]=8'h00; mem['h094A]=8'h00; mem['h094B]=8'h00;
    mem['h094C]=8'h01; mem['h094D]=8'h22; mem['h094E]=8'hFF; mem['h094F]=8'h8A;
    mem['h0950]=8'h09; mem['h0951]=8'h4C; mem['h0952]=8'h02; mem['h0953]=8'h21;
    mem['h0954]=8'hFF; mem['h0955]=8'h8C; mem['h0956]=8'h09; mem['h0957]=8'h00;
    mem['h0958]=8'h00; mem['h0959]=8'h00; mem['h095A]=8'h00; mem['h095B]=8'h00;
    mem['h095C]=8'h00; mem['h095D]=8'h43; mem['h095E]=8'h02; mem['h095F]=8'h25;
    mem['h0960]=8'hFF; mem['h0961]=8'h8E; mem['h0962]=8'h09; mem['h0963]=8'h00;
    mem['h0964]=8'h00; mem['h0965]=8'h00; mem['h0966]=8'h00; mem['h0967]=8'h00;
    mem['h0968]=8'h00; mem['h0969]=8'h50; mem['h096A]=8'h02; mem['h096B]=8'h23;
    mem['h096C]=8'hFF; mem['h096D]=8'h91; mem['h096E]=8'h09; mem['h096F]=8'h00;
    mem['h0970]=8'h00; mem['h0971]=8'h00; mem['h0972]=8'h00; mem['h0973]=8'h00;
    mem['h0974]=8'h00; mem['h0975]=8'h41; mem['h0976]=8'h00; mem['h0977]=8'h42;
    mem['h0978]=8'h43; mem['h0979]=8'h00; mem['h097A]=8'h42; mem['h097B]=8'h00;
    mem['h097C]=8'h43; mem['h097D]=8'h00; mem['h097E]=8'h44; mem['h097F]=8'h45;
    mem['h0980]=8'h00; mem['h0981]=8'h44; mem['h0982]=8'h00; mem['h0983]=8'h45;
    mem['h0984]=8'h00; mem['h0985]=8'h46; mem['h0986]=8'h00; mem['h0987]=8'h48;
    mem['h0988]=8'h4C; mem['h0989]=8'h00; mem['h098A]=8'h48; mem['h098B]=8'h00;
    mem['h098C]=8'h4C; mem['h098D]=8'h00; mem['h098E]=8'h50; mem['h098F]=8'h43;
    mem['h0990]=8'h00; mem['h0991]=8'h53; mem['h0992]=8'h50; mem['h0993]=8'h00;
    mem['h0994]=8'h3E; mem['h0995]=8'h00; mem['h0996]=8'hD3; mem['h0997]=8'h01;
    mem['h0998]=8'h3E; mem['h0999]=8'h00; mem['h099A]=8'hD3; mem['h099B]=8'h01;
    mem['h099C]=8'h3E; mem['h099D]=8'h00; mem['h099E]=8'hD3; mem['h099F]=8'h01;
    mem['h09A0]=8'h3E; mem['h09A1]=8'h40; mem['h09A2]=8'hD3; mem['h09A3]=8'h01;
    mem['h09A4]=8'h3E; mem['h09A5]=8'h4E; mem['h09A6]=8'hD3; mem['h09A7]=8'h01;
    mem['h09A8]=8'h3E; mem['h09A9]=8'h37; mem['h09AA]=8'hD3; mem['h09AB]=8'h01;
    mem['h09AC]=8'hC9; mem['h09AD]=8'hDB; mem['h09AE]=8'h01; mem['h09AF]=8'hE6;
    mem['h09B0]=8'h02; mem['h09B1]=8'hCA; mem['h09B2]=8'hAD; mem['h09B3]=8'h09;
    mem['h09B4]=8'hDB; mem['h09B5]=8'h00; mem['h09B6]=8'hC9; mem['h09B7]=8'hDB;
    mem['h09B8]=8'h01; mem['h09B9]=8'hE6; mem['h09BA]=8'h02; mem['h09BB]=8'hC9;
    mem['h09BC]=8'hF5; mem['h09BD]=8'hDB; mem['h09BE]=8'h01; mem['h09BF]=8'hE6;
    mem['h09C0]=8'h01; mem['h09C1]=8'hCA; mem['h09C2]=8'hBD; mem['h09C3]=8'h09;
    mem['h09C4]=8'hF1; mem['h09C5]=8'hD3; mem['h09C6]=8'h00; mem['h09C7]=8'hC9;
    mem['h09C8]=8'h00; mem['h09C9]=8'h00; mem['h09CA]=8'h00; mem['h09CB]=8'h00;
end
